pulp-platform/fmc_peripheral_boards/05_FMC_4_Hyperram_32MB/Documentation/FMC_4Hyperram_board_LAY.PDF

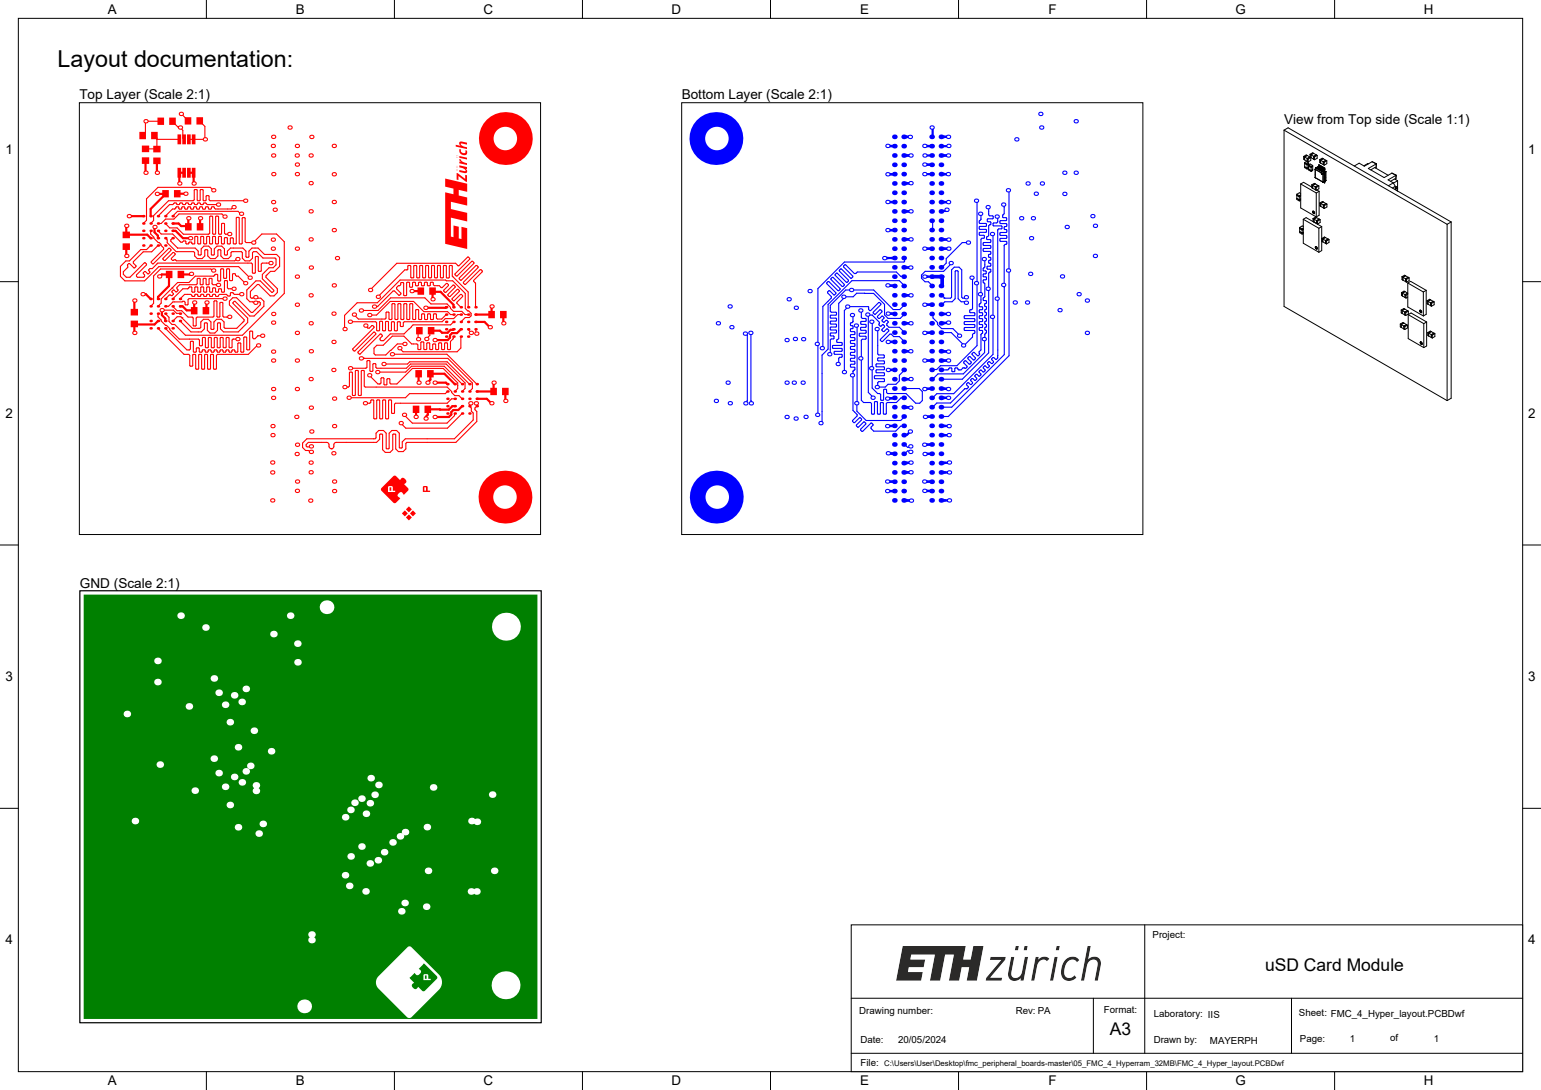
[picture p35: page 1]

View from Top side (Scale 1:1)

Project: uSD Card Module

Drawing number: Rev: PA Date: 20/05/2024 | Format: | Laboratory: IIS Drawn by: MAYERPH | Sheet: FMC_4_Hyper_layout.PCBDwf of A3 Page: 1 1

File:
C:\Users\User\Desktop\fmc_peripheral_boards-master\05_FMC_4_Hyperram_32MB\FMC_4_Hyper_layout.PCBDwf
