pulp-platform/fmc_peripheral_boards/05_FMC_4_Hyperram_32MB/Documentation/FMC_4Hyperram_board_SCH.pdf

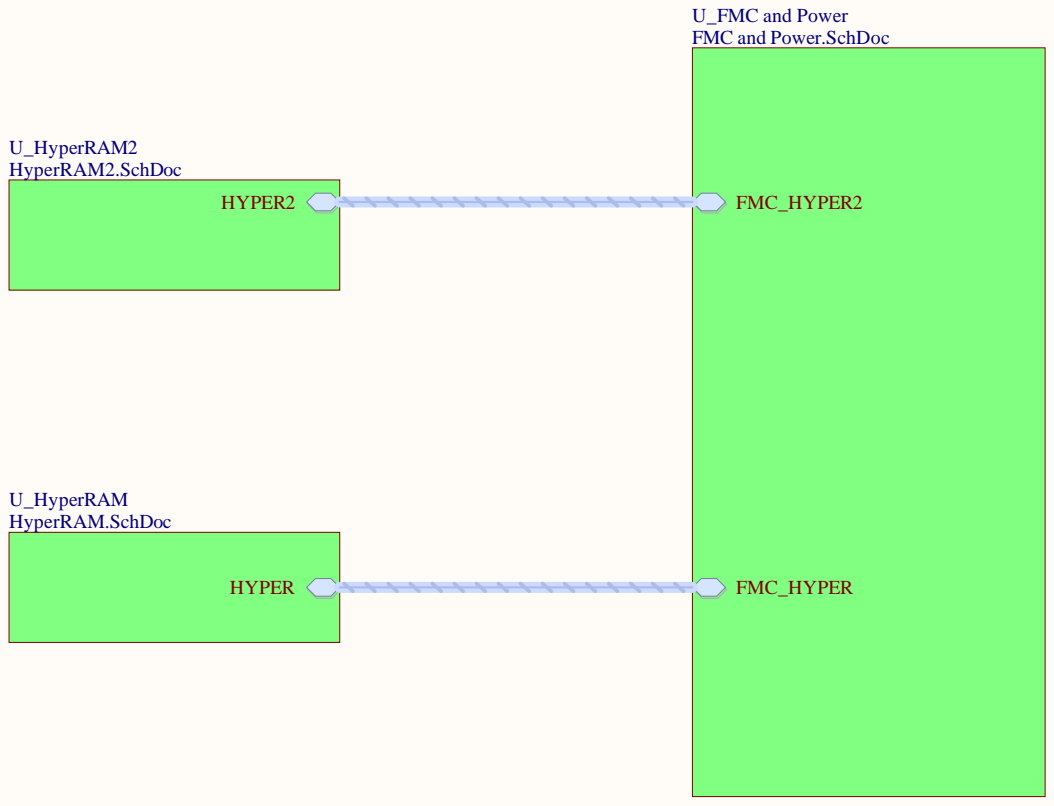
[picture p36: page 1]

U_FMC and Power
FMC and Power.SchDoc

Project: Pulp FMC Sensor Board

Drawing number: Rev: * Date: 20/05/2024 14:07:33 | Format: A4 Q | Laboratory: Microelectronics Design Center Drawn by: A. Blanco Fontao | Sheet: Page 1 of 7

C:\Users\User\Desktop\fmc_peripheral_boards-master\05_FMC_4_Hyperram_32MB\FMC_4Hyperram_board.SchDoc

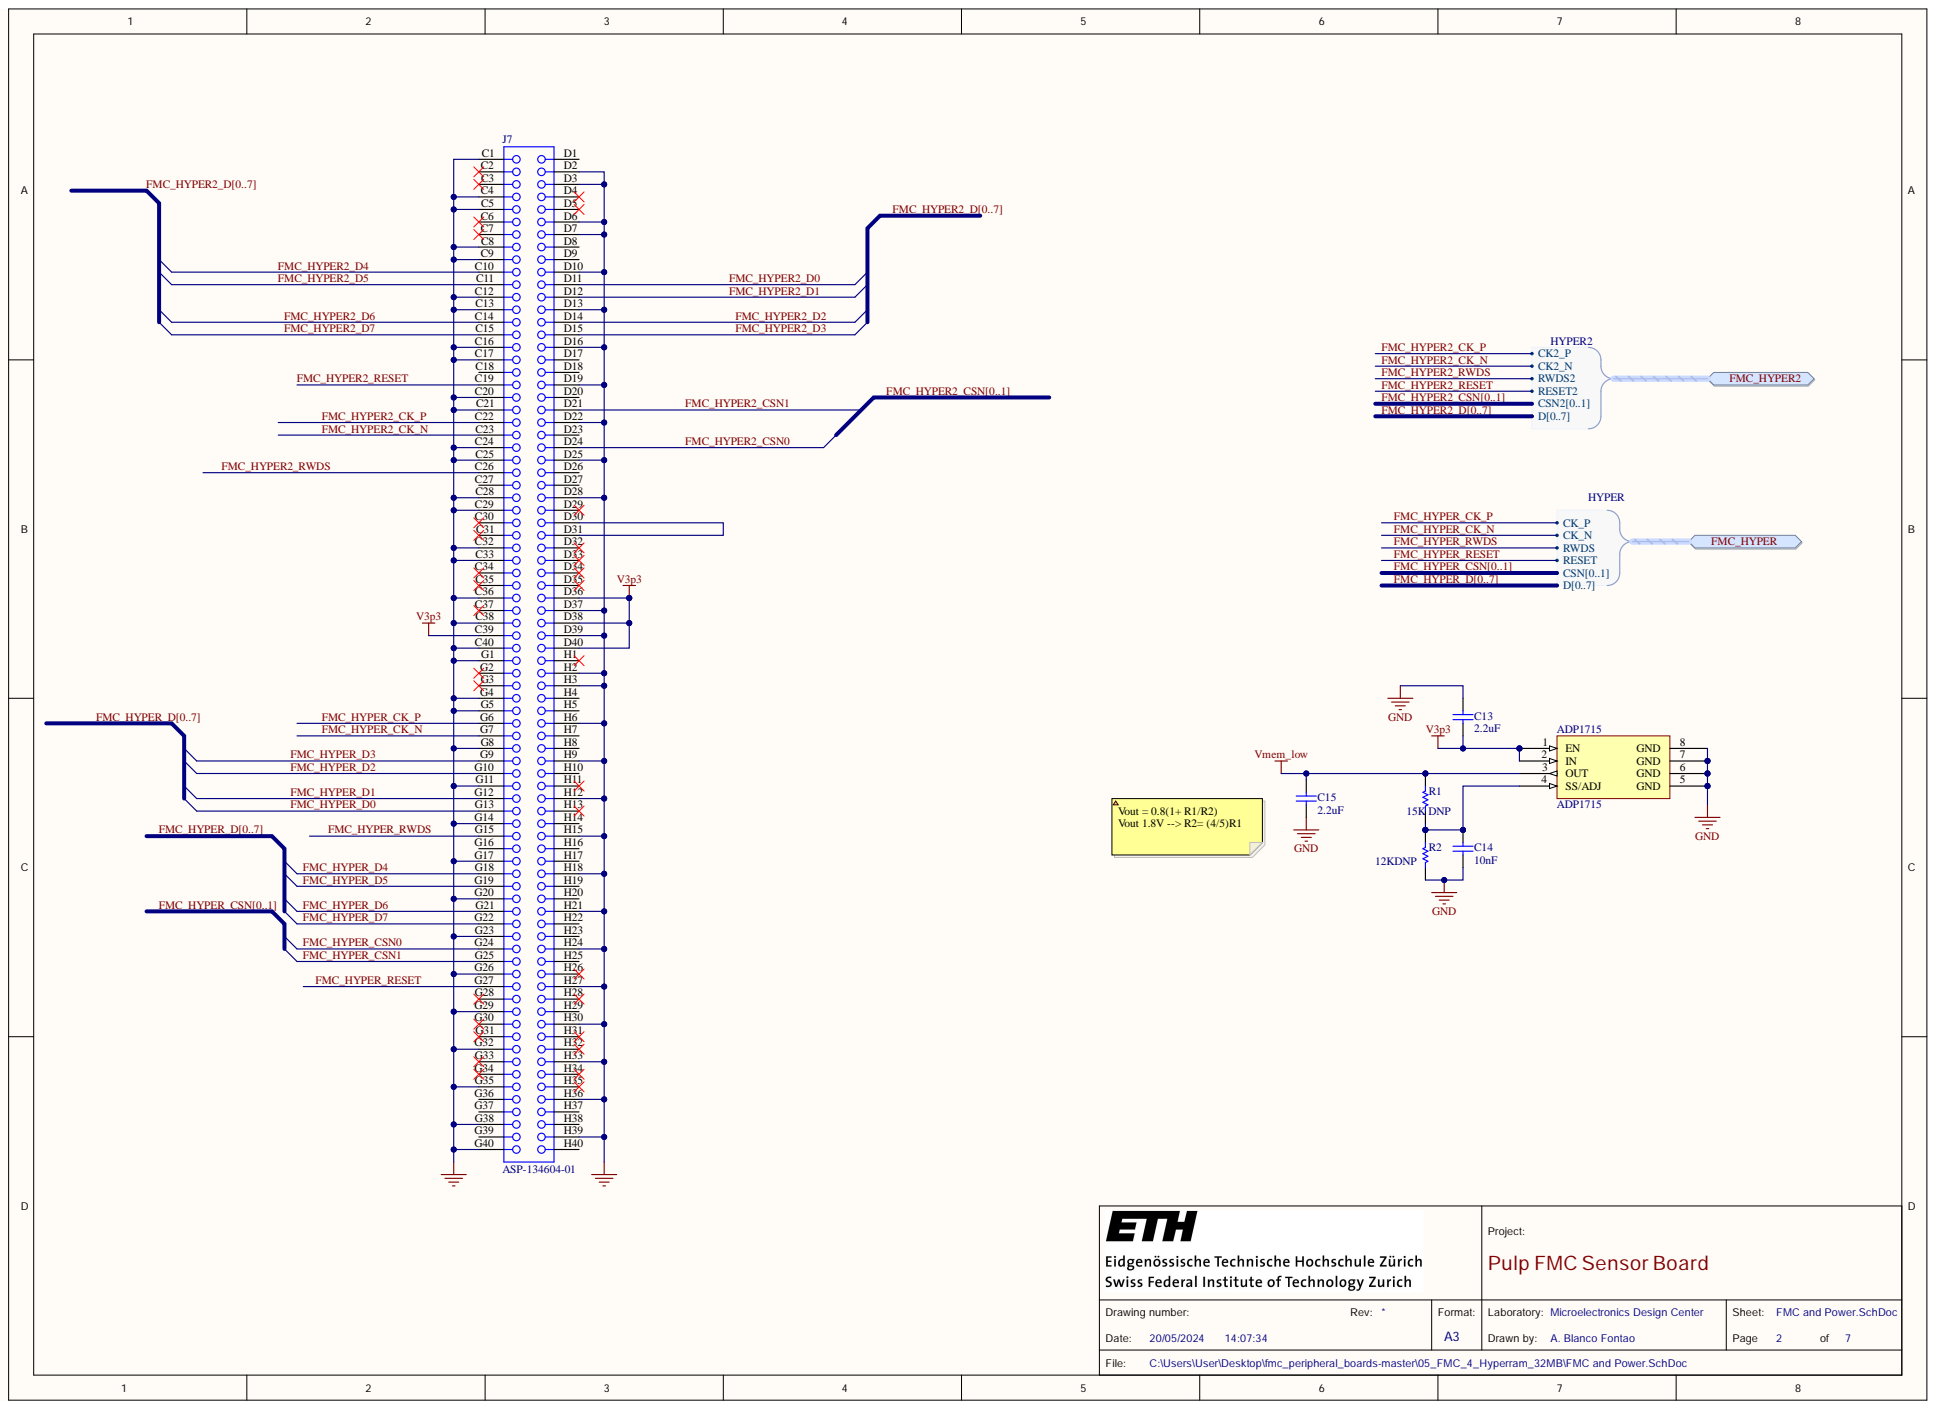
[picture p37: page 2]

C2 | | D2
C3 | | D3
C4 | | D4
C5 | | D5
C6 | | D6
C7 | | D7
C8 | | D8
C9 | | D9
C10 C11 C12 | | D10

C13
C14 C15 C16 | D14 D15 D16

C21 | | D21 D22
C22 C23 C24

C25
C26 C27 | | D26

C28 | | D28
C29 | | D29
C30 | | D30
C31 | | D31
C32 | | D32 | | V3p3
C33 | | D33
C34 | | D34
C35 | | D35
C36 | | D36
C37 | | D37
C38 | | D38
C39 | | D39
C40 | | D40
G1 | | H1
G2 | | H2
G3 | | H3
G4 | | H4

G6 G7 G8 | H6 | GND

G17 | | H17
G18 G19 G20 | | H18

G29 | | H29
G30 | | H30
G31 | | H31
G32 | | H32
G33 | | H33
G34 | | H34
G35 | | H35
G36 | | H36
G37 | | H37
G38 | | H38
G39 | | H39
G40 | | H40

Project: Pulp FMC Sensor Board

Drawing number: Rev: * Date: 20/05/2024 14:07:34 | Format: A3 | Laboratory: Microelectronics Design Center Drawn by: A. Blanco Fontao | Sheet: FMC and Power.SchDoc Page 2 of 7

C:\Users\User\Desktop\fmc_peripheral_boards-master\05_FMC_4_Hyperram_32MB\FMC and Power.SchDoc

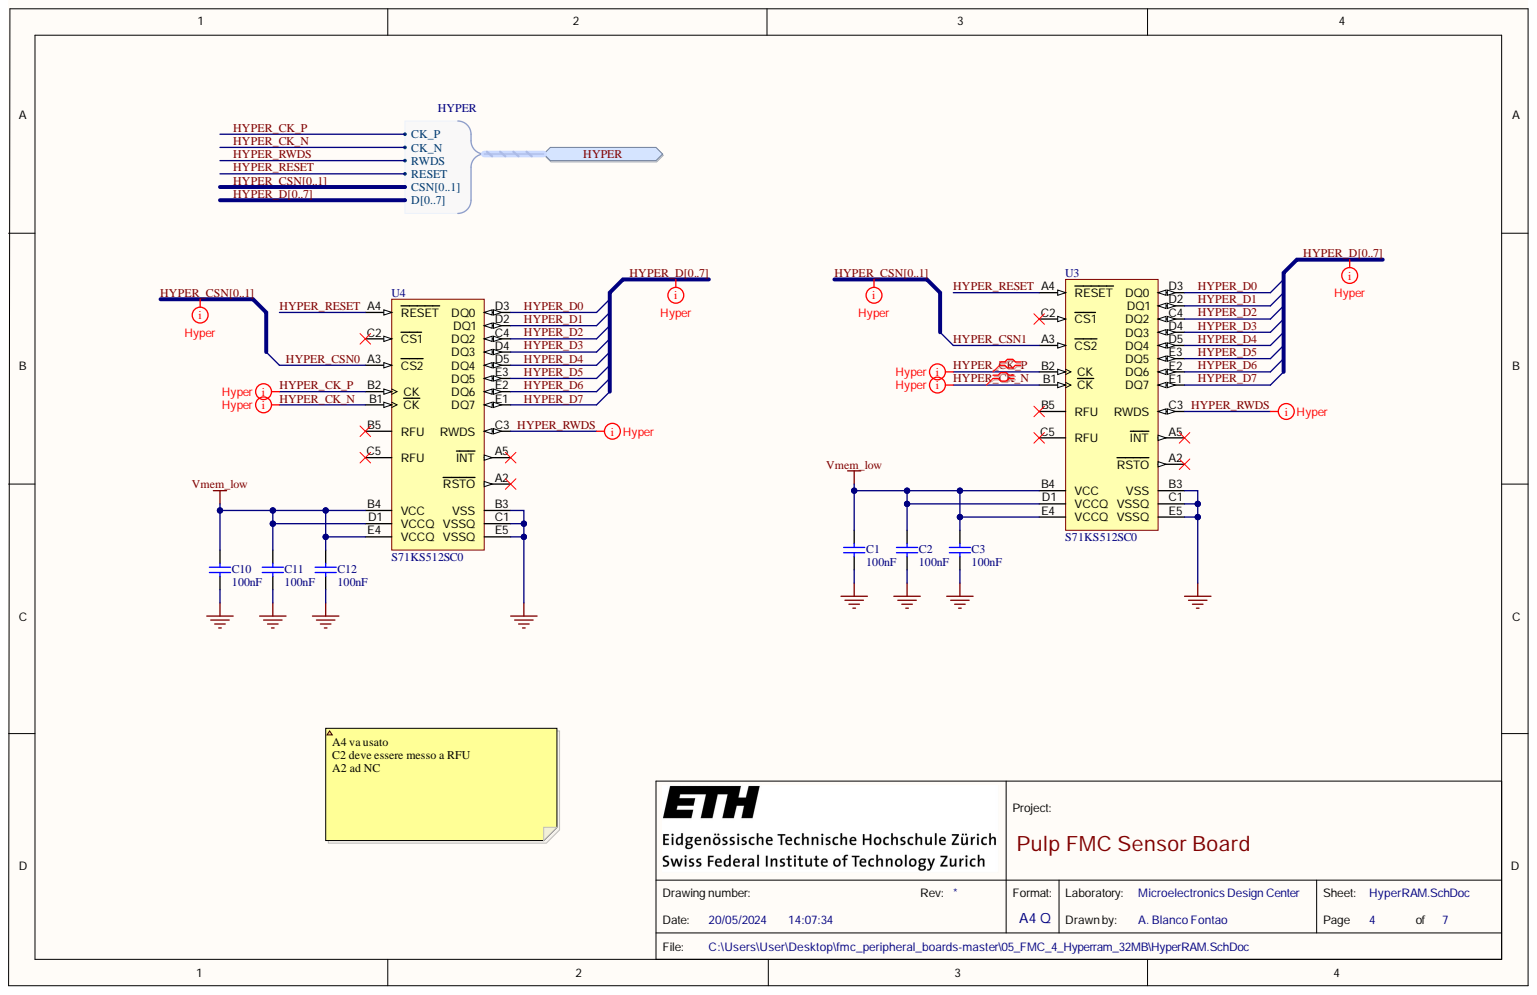
[picture p38: page 3]

A4 va usato
C2 deve essere messo a RFU

Project: Pulp FMC Sensor Board

Drawing number: Rev: * Date: 20/05/2024 14:07:34 | Format: A4 Q | Laboratory: Microelectronics Design Center Drawn by: A. Blanco Fontao | Sheet: HyperRAM.SchDoc Page 4 of 7

C:\Users\User\Desktop\fmc_peripheral_boards-master\05_FMC_4_Hyperram_32MB\HyperRAM.SchDoc

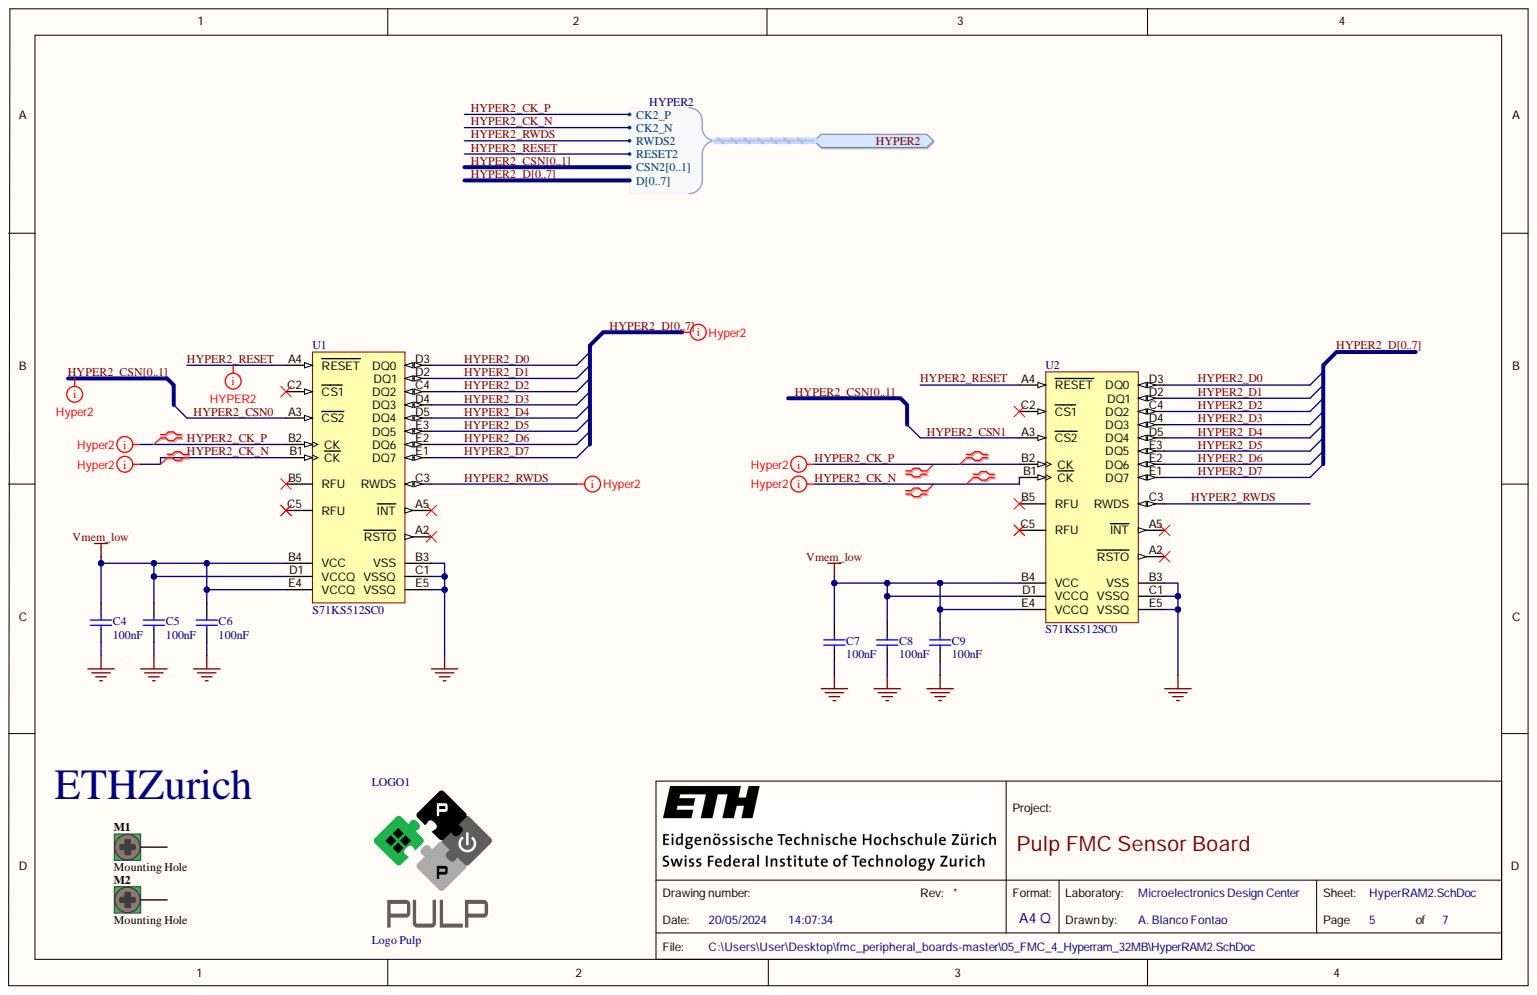
[picture p39: page 4]

Project: Pulp FMC Sensor Board

Drawing number: Rev: * Date: 20/05/2024 14:07:34 | Format: A4 Q | Laboratory: Microelectronics Design Center Drawn by: A. Blanco Fontao | Sheet: HyperRAM2.SchDoc Page 5 of 7

C:\Users\User\Desktop\fmc_peripheral_boards-master\05_FMC_4_Hyperram_32MB\HyperRAM2.SchDoc

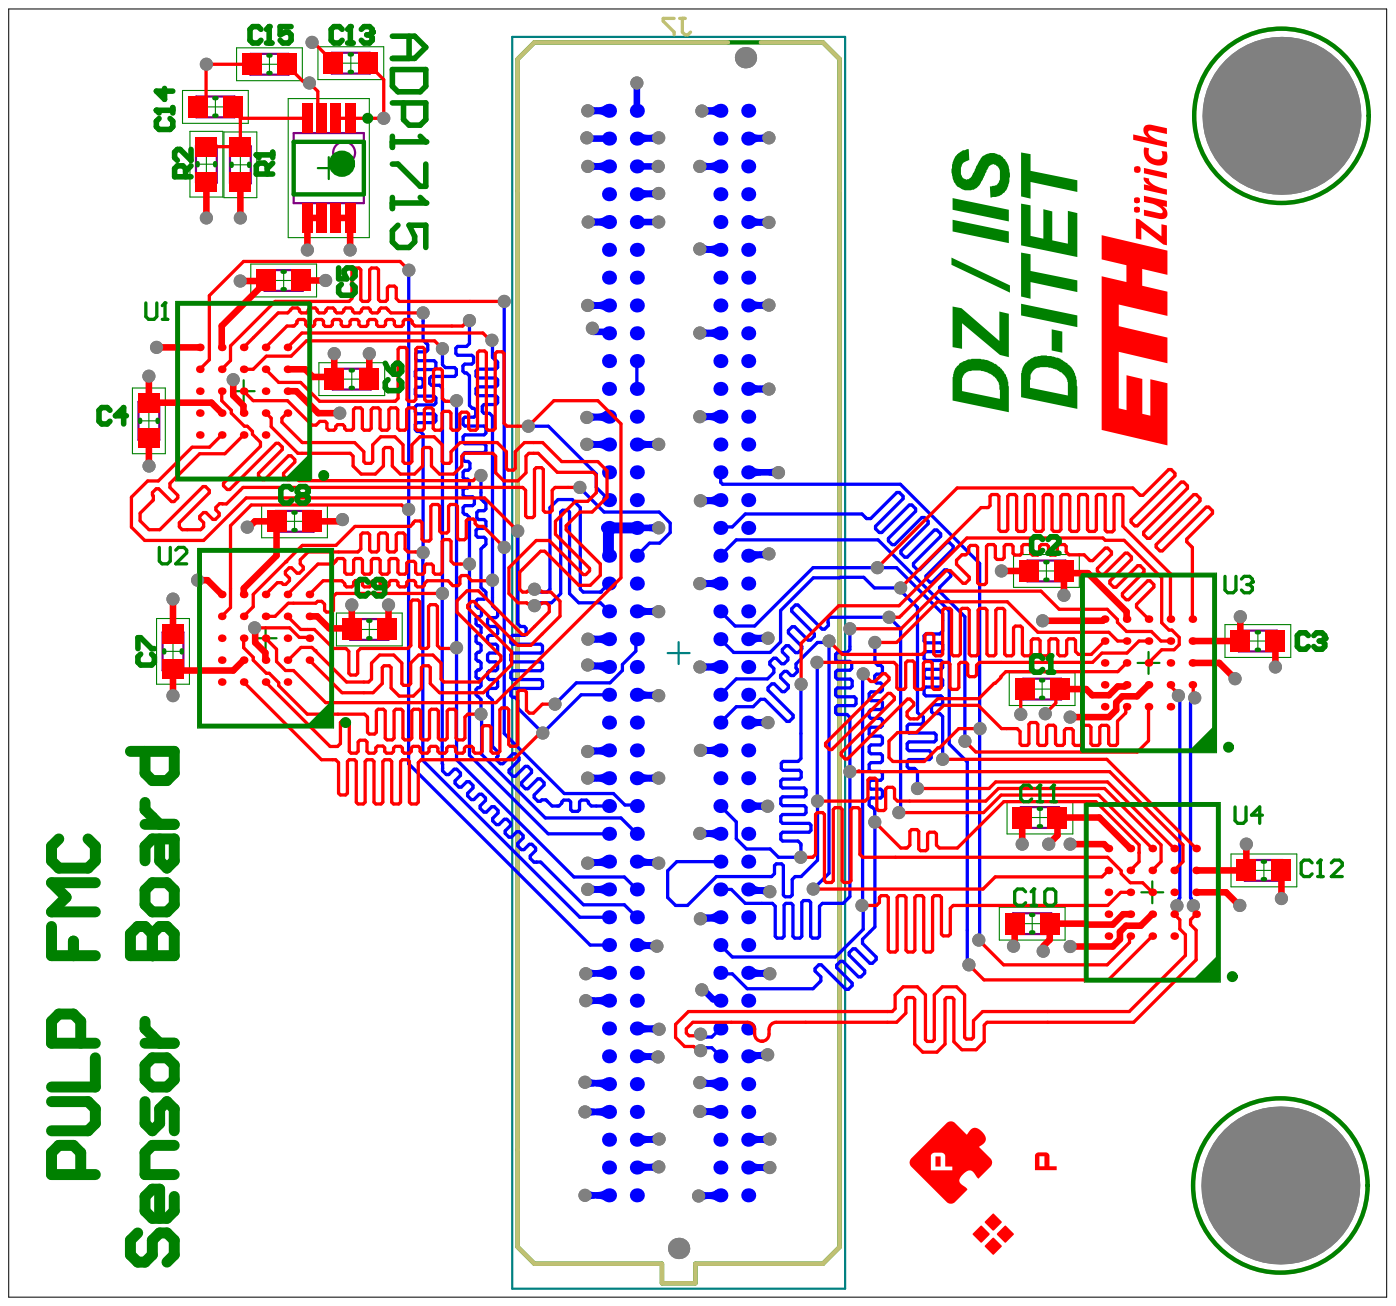
[picture p40: page 5]
