pulp-platform/fmc_peripheral_boards/01_Carrier_Board/Documentation/FPGA_Peripheral_Board_CON.PDF

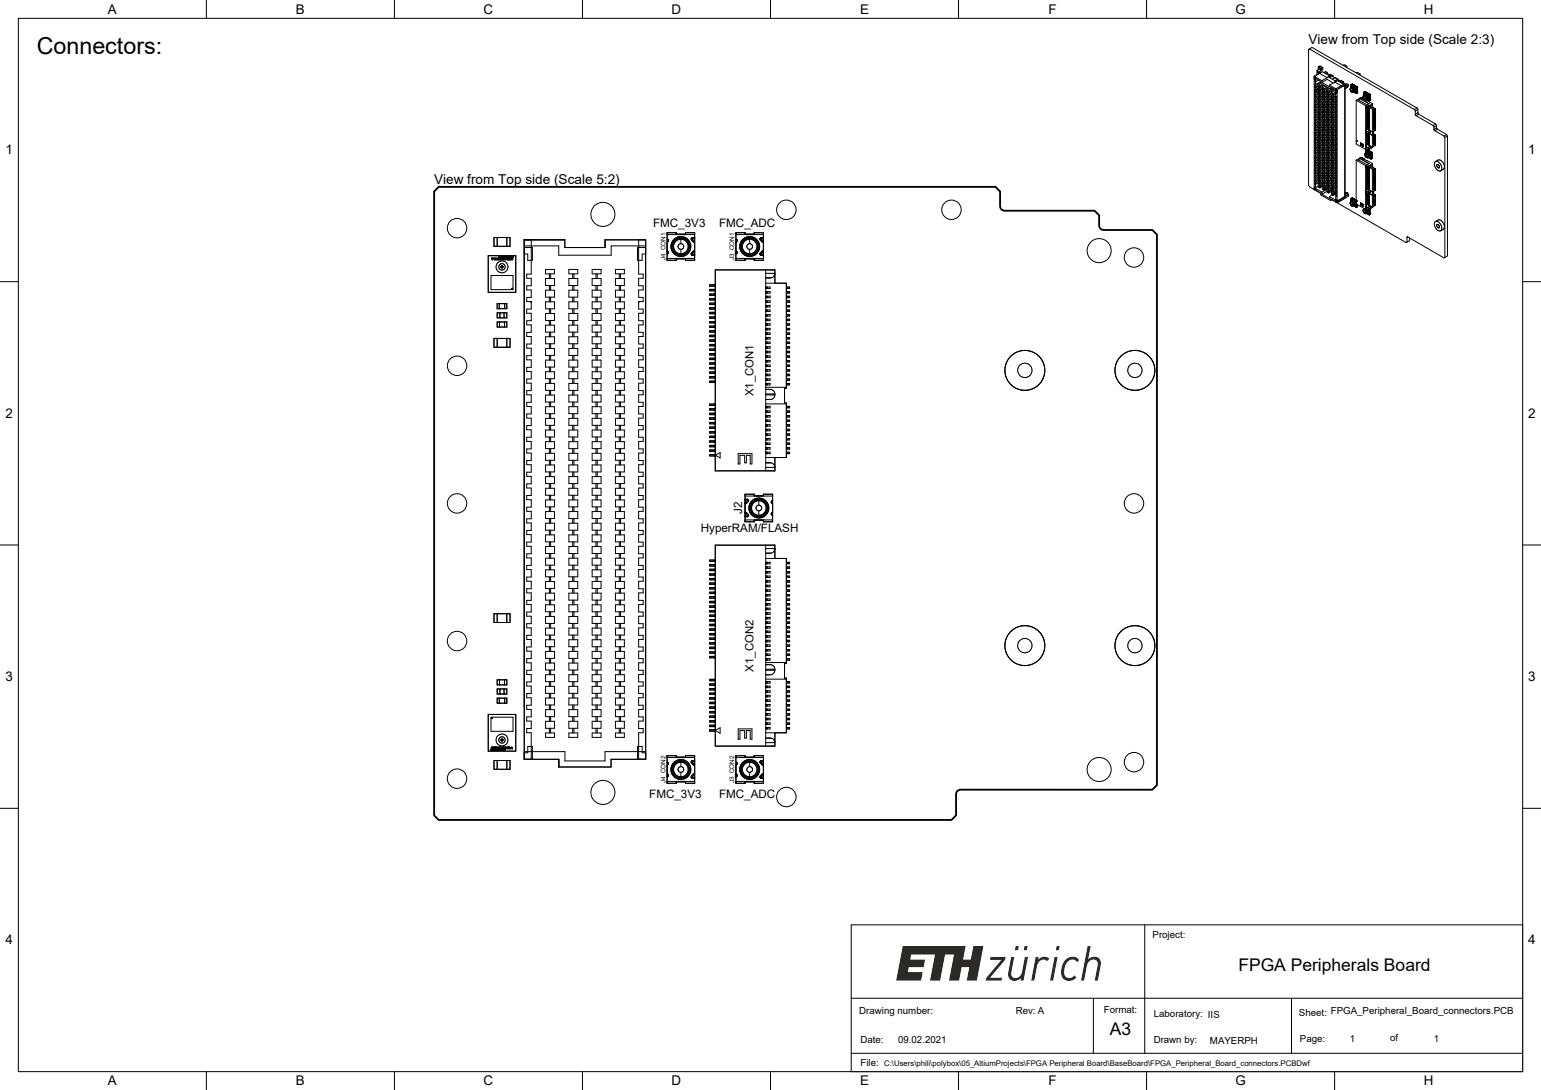
[picture p43: page 1]

View from Top side (Scale 2:3)

View from Top side (Scale 5:2)

File:
C:\Users\phili\polybox\05_AltiumProjects\FPGA Peripheral Board\BaseBoard\FPGA_Peripheral_Board_connectors.PCBDwf
