pulp-platform/fmc_peripheral_boards/01_Carrier_Board/Documentation/FPGA_Peripheral_Board_FAB.PDF

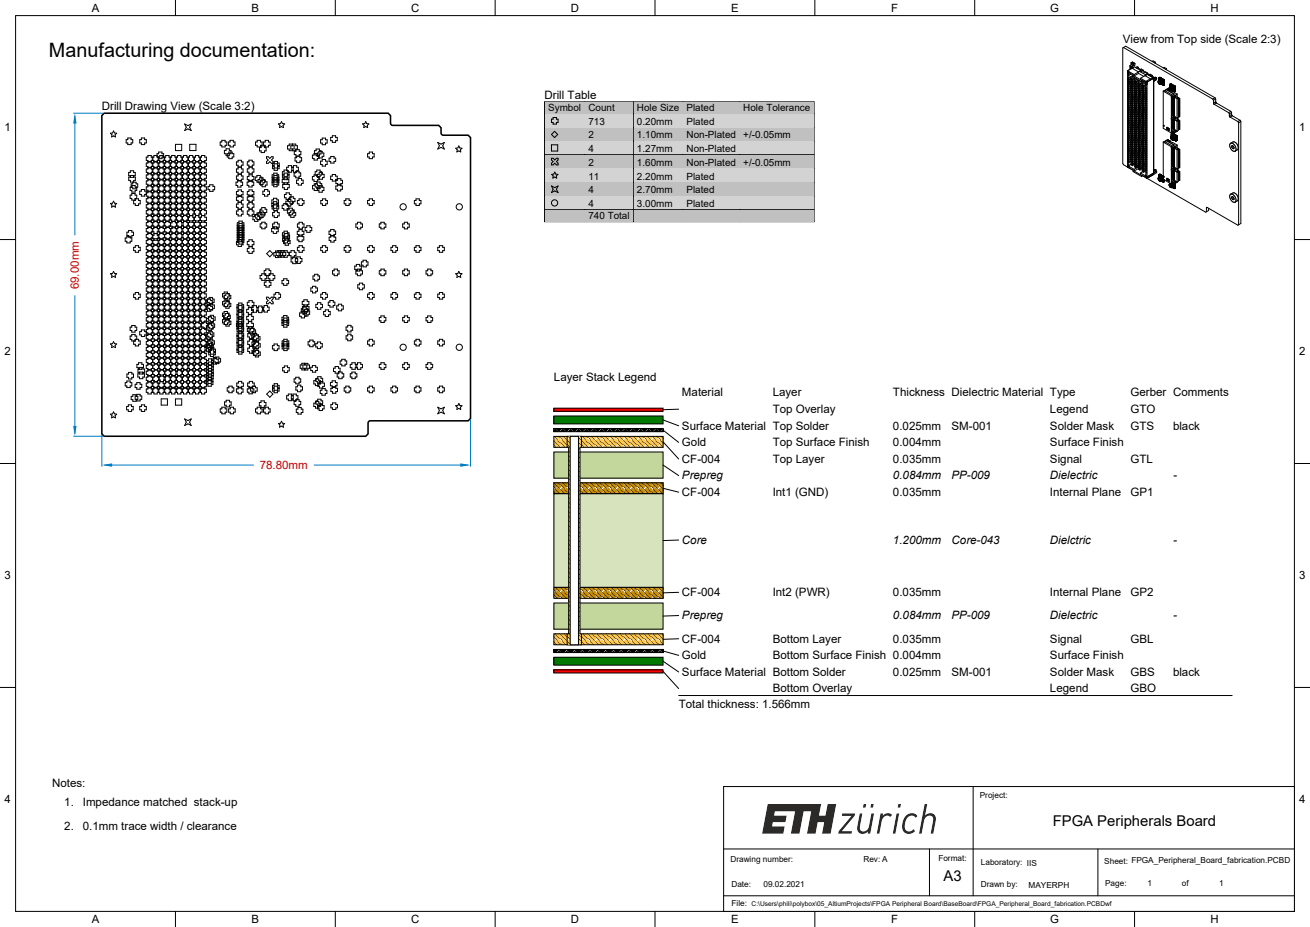
[picture p44: page 1]

View from Top side (Scale 2:3)

Drill Drawing View (Scale 3:2)

Notes:
1. Impedance matched stack-up

File:
C:\Users\phili\polybox\05_AltiumProjects\FPGA Peripheral Board\BaseBoard\FPGA_Peripheral_Board_fabrication.PCBDwf
