pulp-platform/fmc_peripheral_boards/01_Carrier_Board/Documentation/FPGA_Peripheral_Board_LAY.PDF

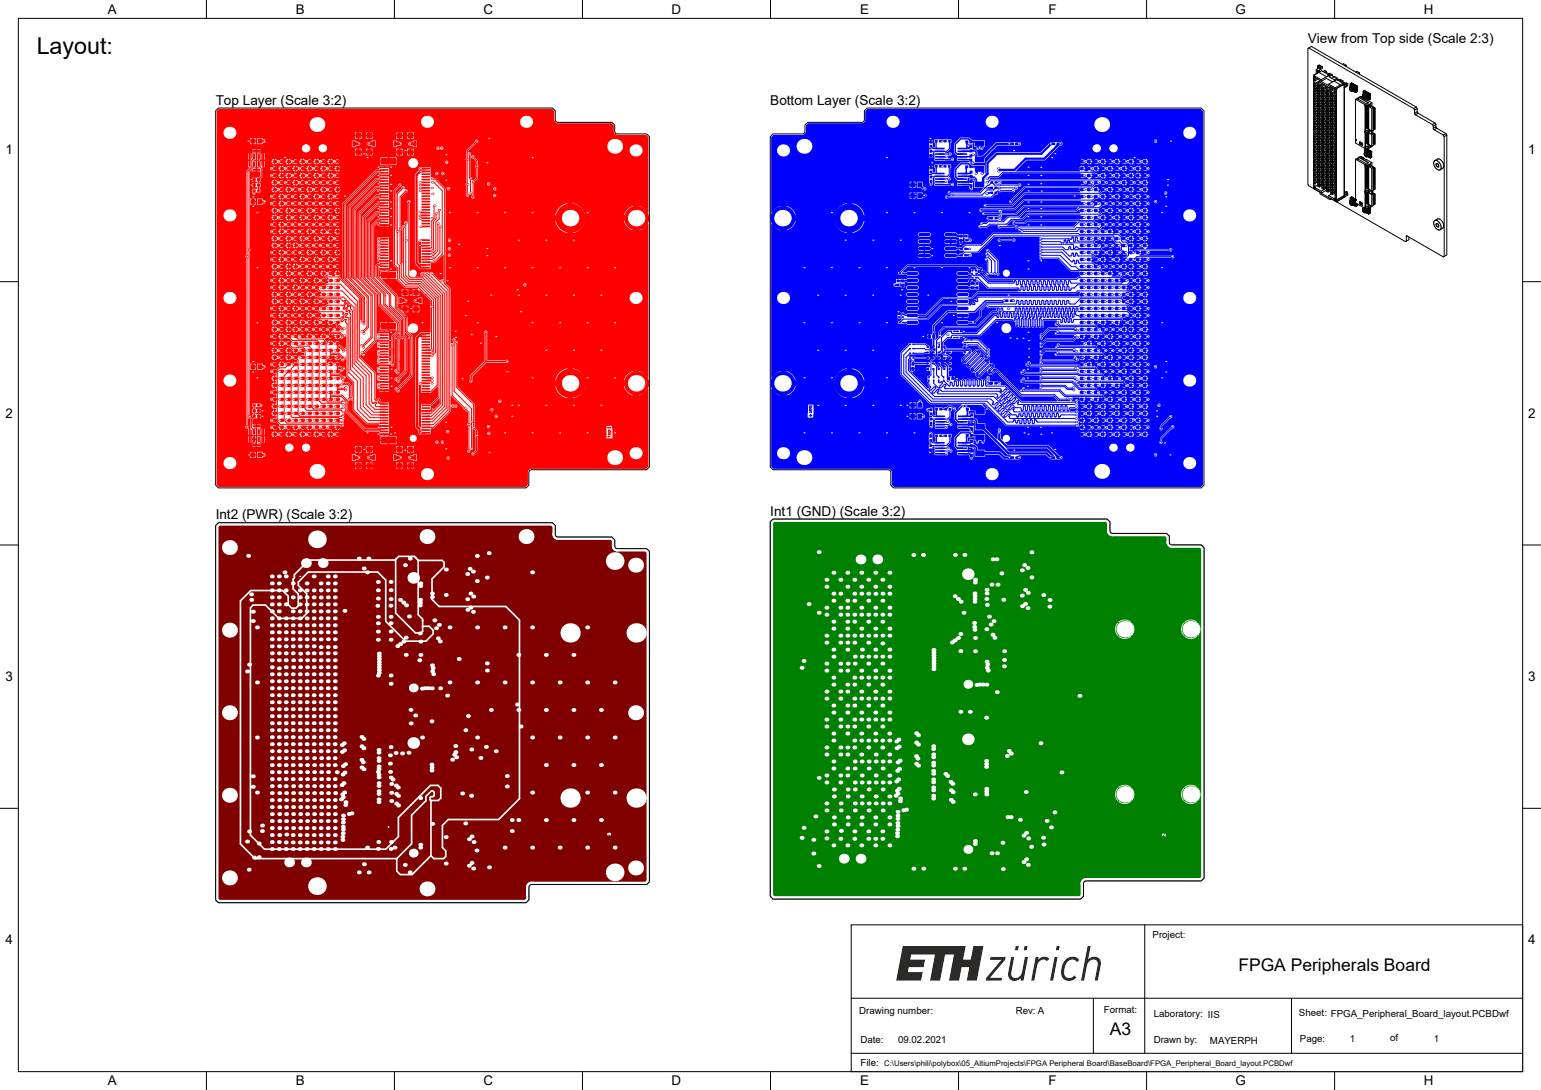
[picture p45: page 1]

View from Top side (Scale 2:3)

File:
C:\Users\phili\polybox\05_AltiumProjects\FPGA Peripheral Board\BaseBoard\FPGA_Peripheral_Board_layout.PCBDwf
