pulp-platform/fmc_peripheral_boards/01_Carrier_Board/Documentation/FPGA_Peripheral_Board_SCH.PDF

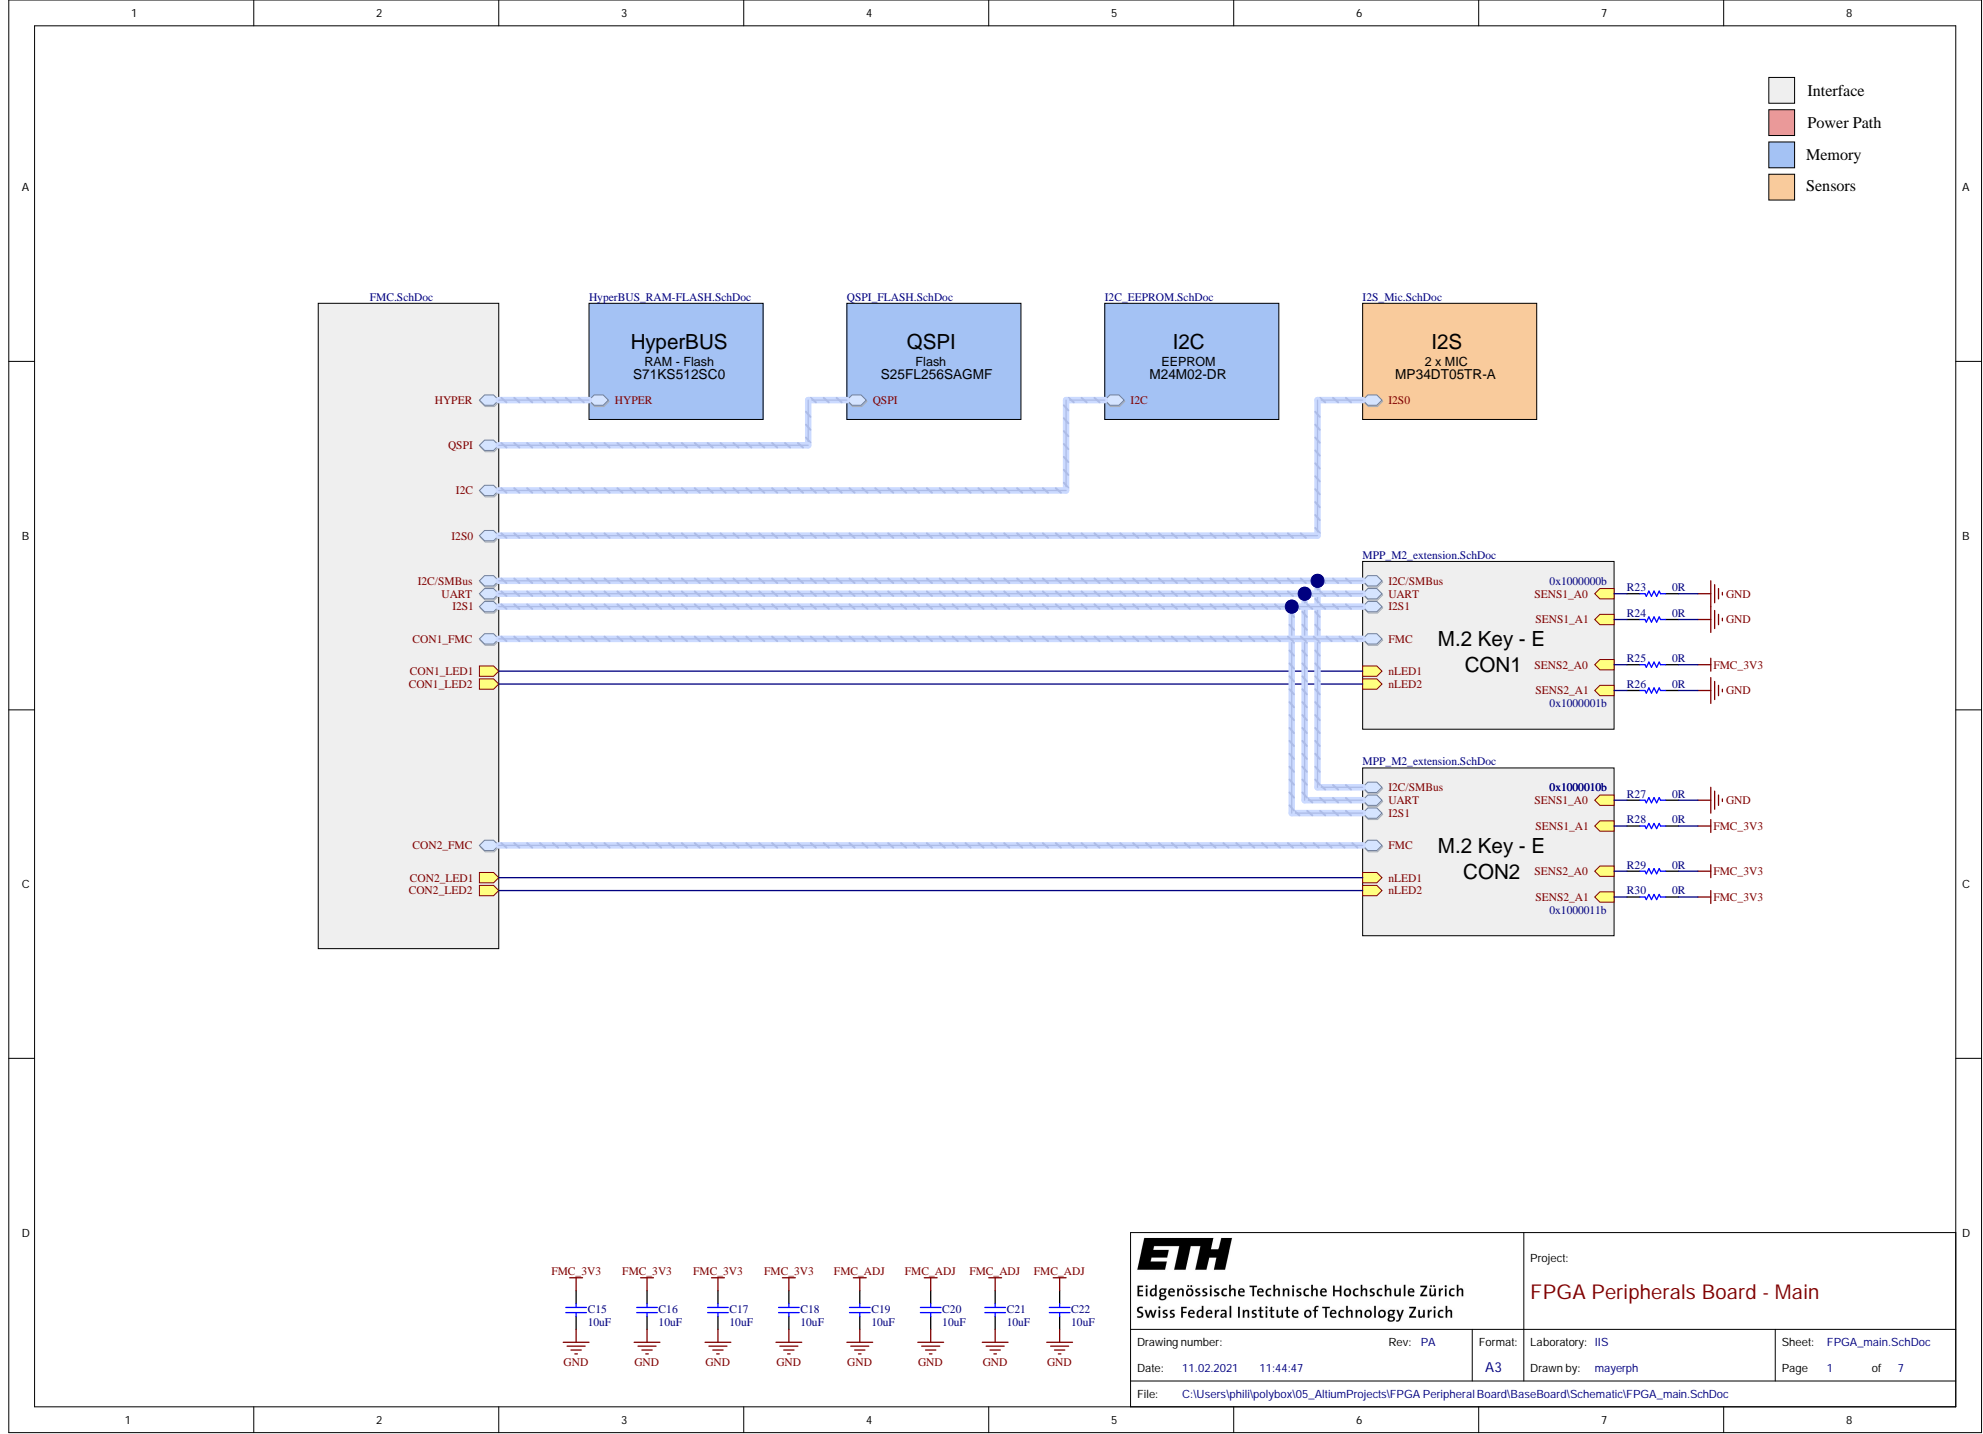
[picture p46: page 1]

FMC.SchDoc HyperBUS_RAM-FLASH.SchDoc QSPI_FLASH.SchDoc I2C_EEPROM.SchDoc I2S_Mic.SchDoc

Project: FPGA Peripherals Board - Main

Drawing number: Rev: PA Date: 11.02.2021 11:44:47 | Format: A3 | Laboratory: IIS Drawn by: mayerph | Sheet: FPGA_main.SchDoc Page 1 of 7

C:\Users\phili\polybox\05_AltiumProjects\FPGA Peripheral Board\BaseBoard\Schematic\FPGA_main.SchDoc

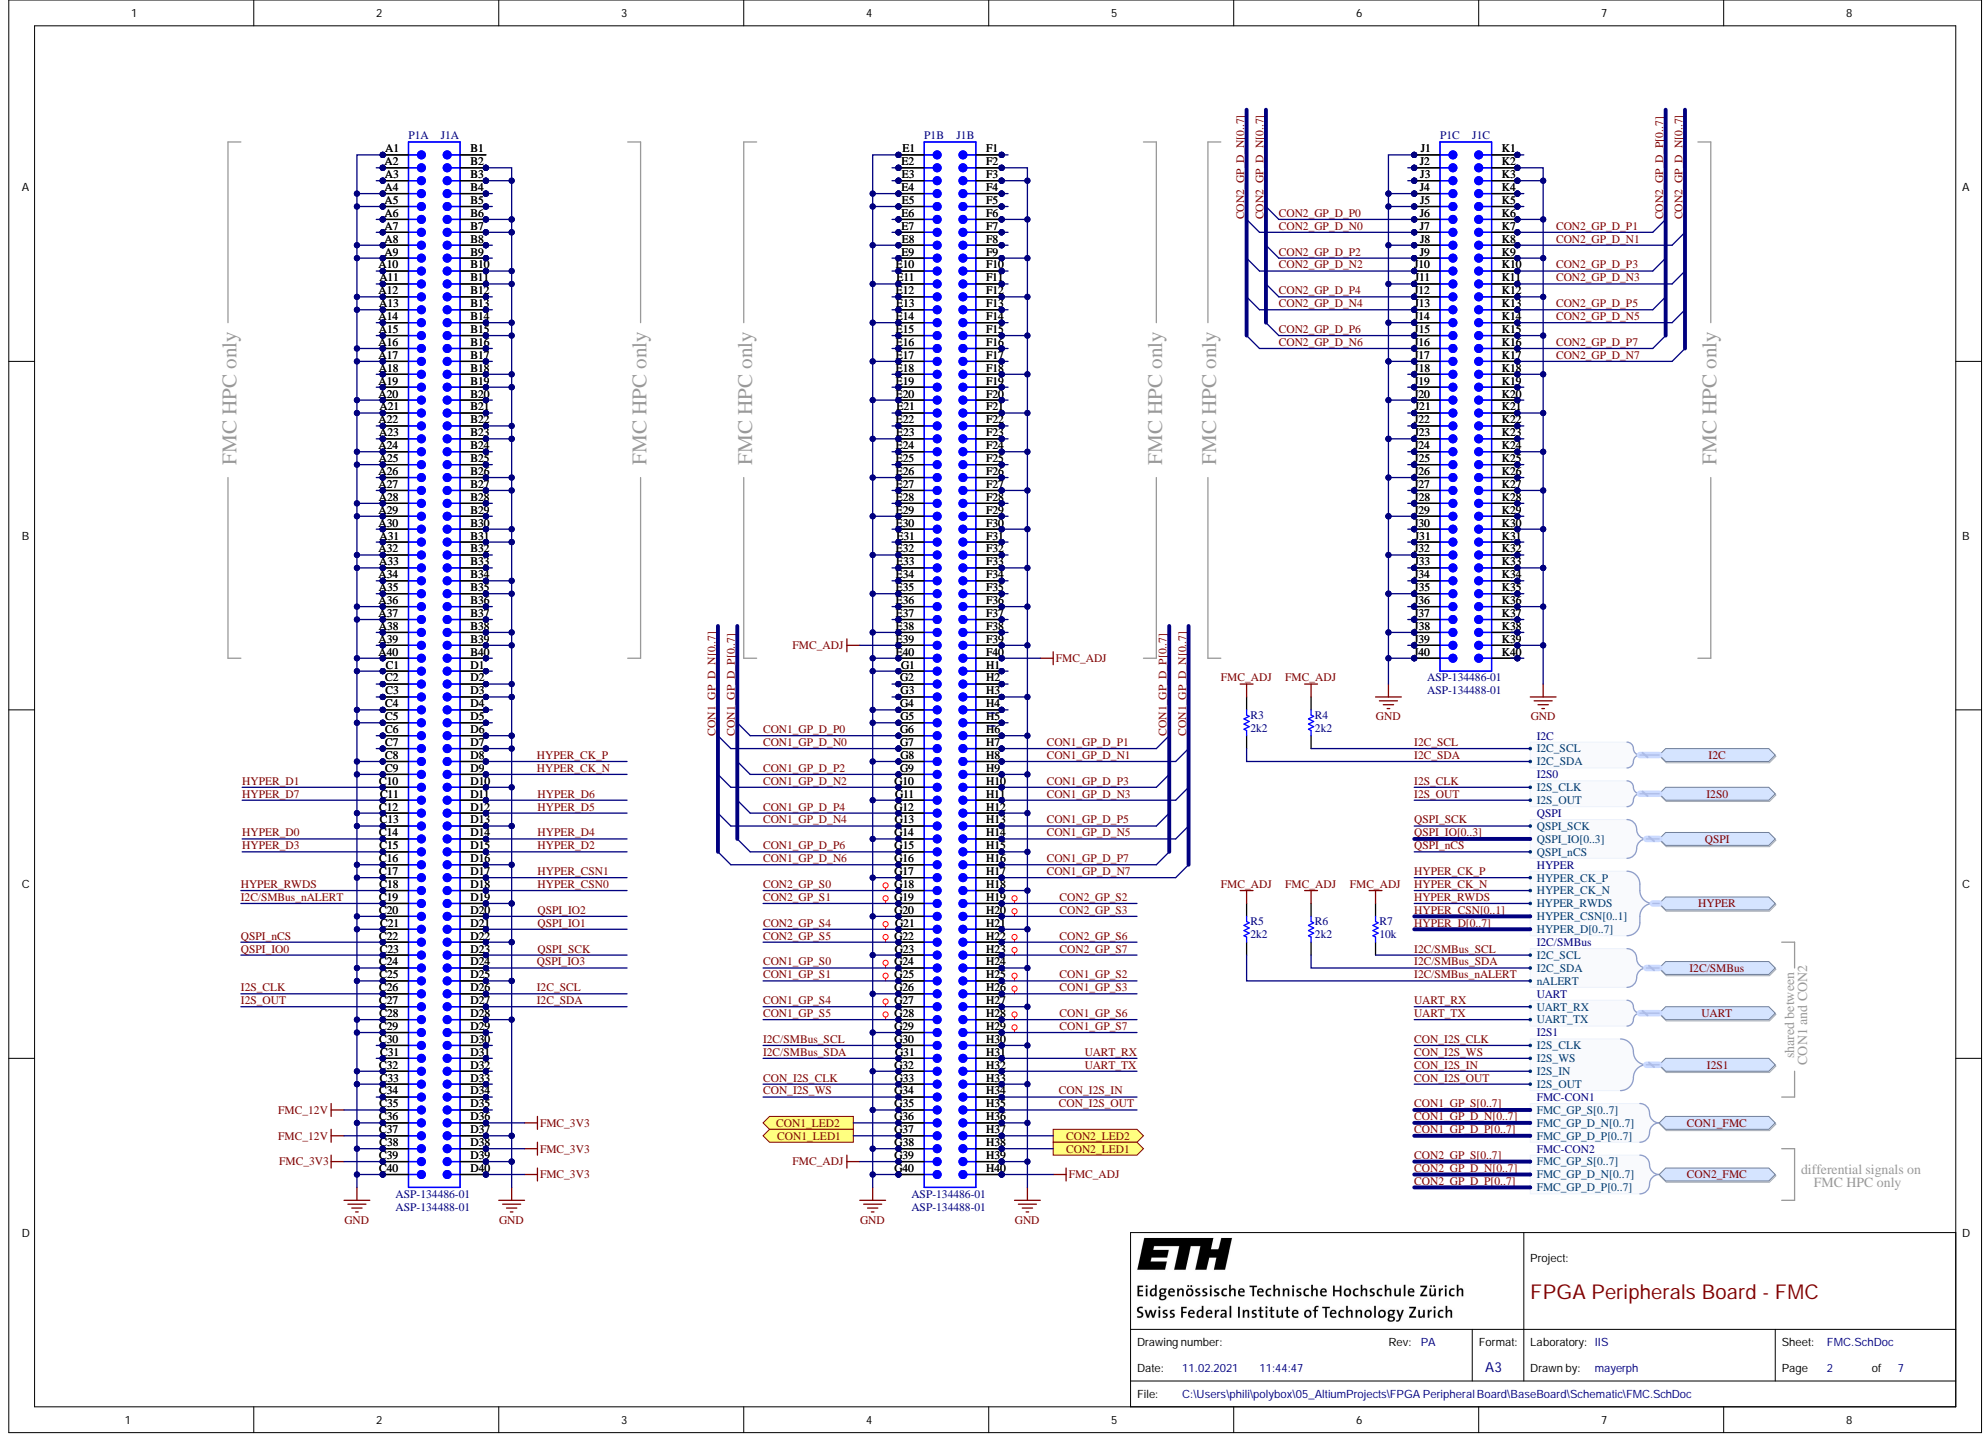
[picture p47: page 2]

CON1 and CON2 differential signals on FMC HPC only

Project: FPGA Pe rip h e rals Bo a rd - FMC

Drawin g n umb er: | Forma t: | L a b oratory: IIS Drawn by: | Sh eet: FMC.SchDoc Page 2 of

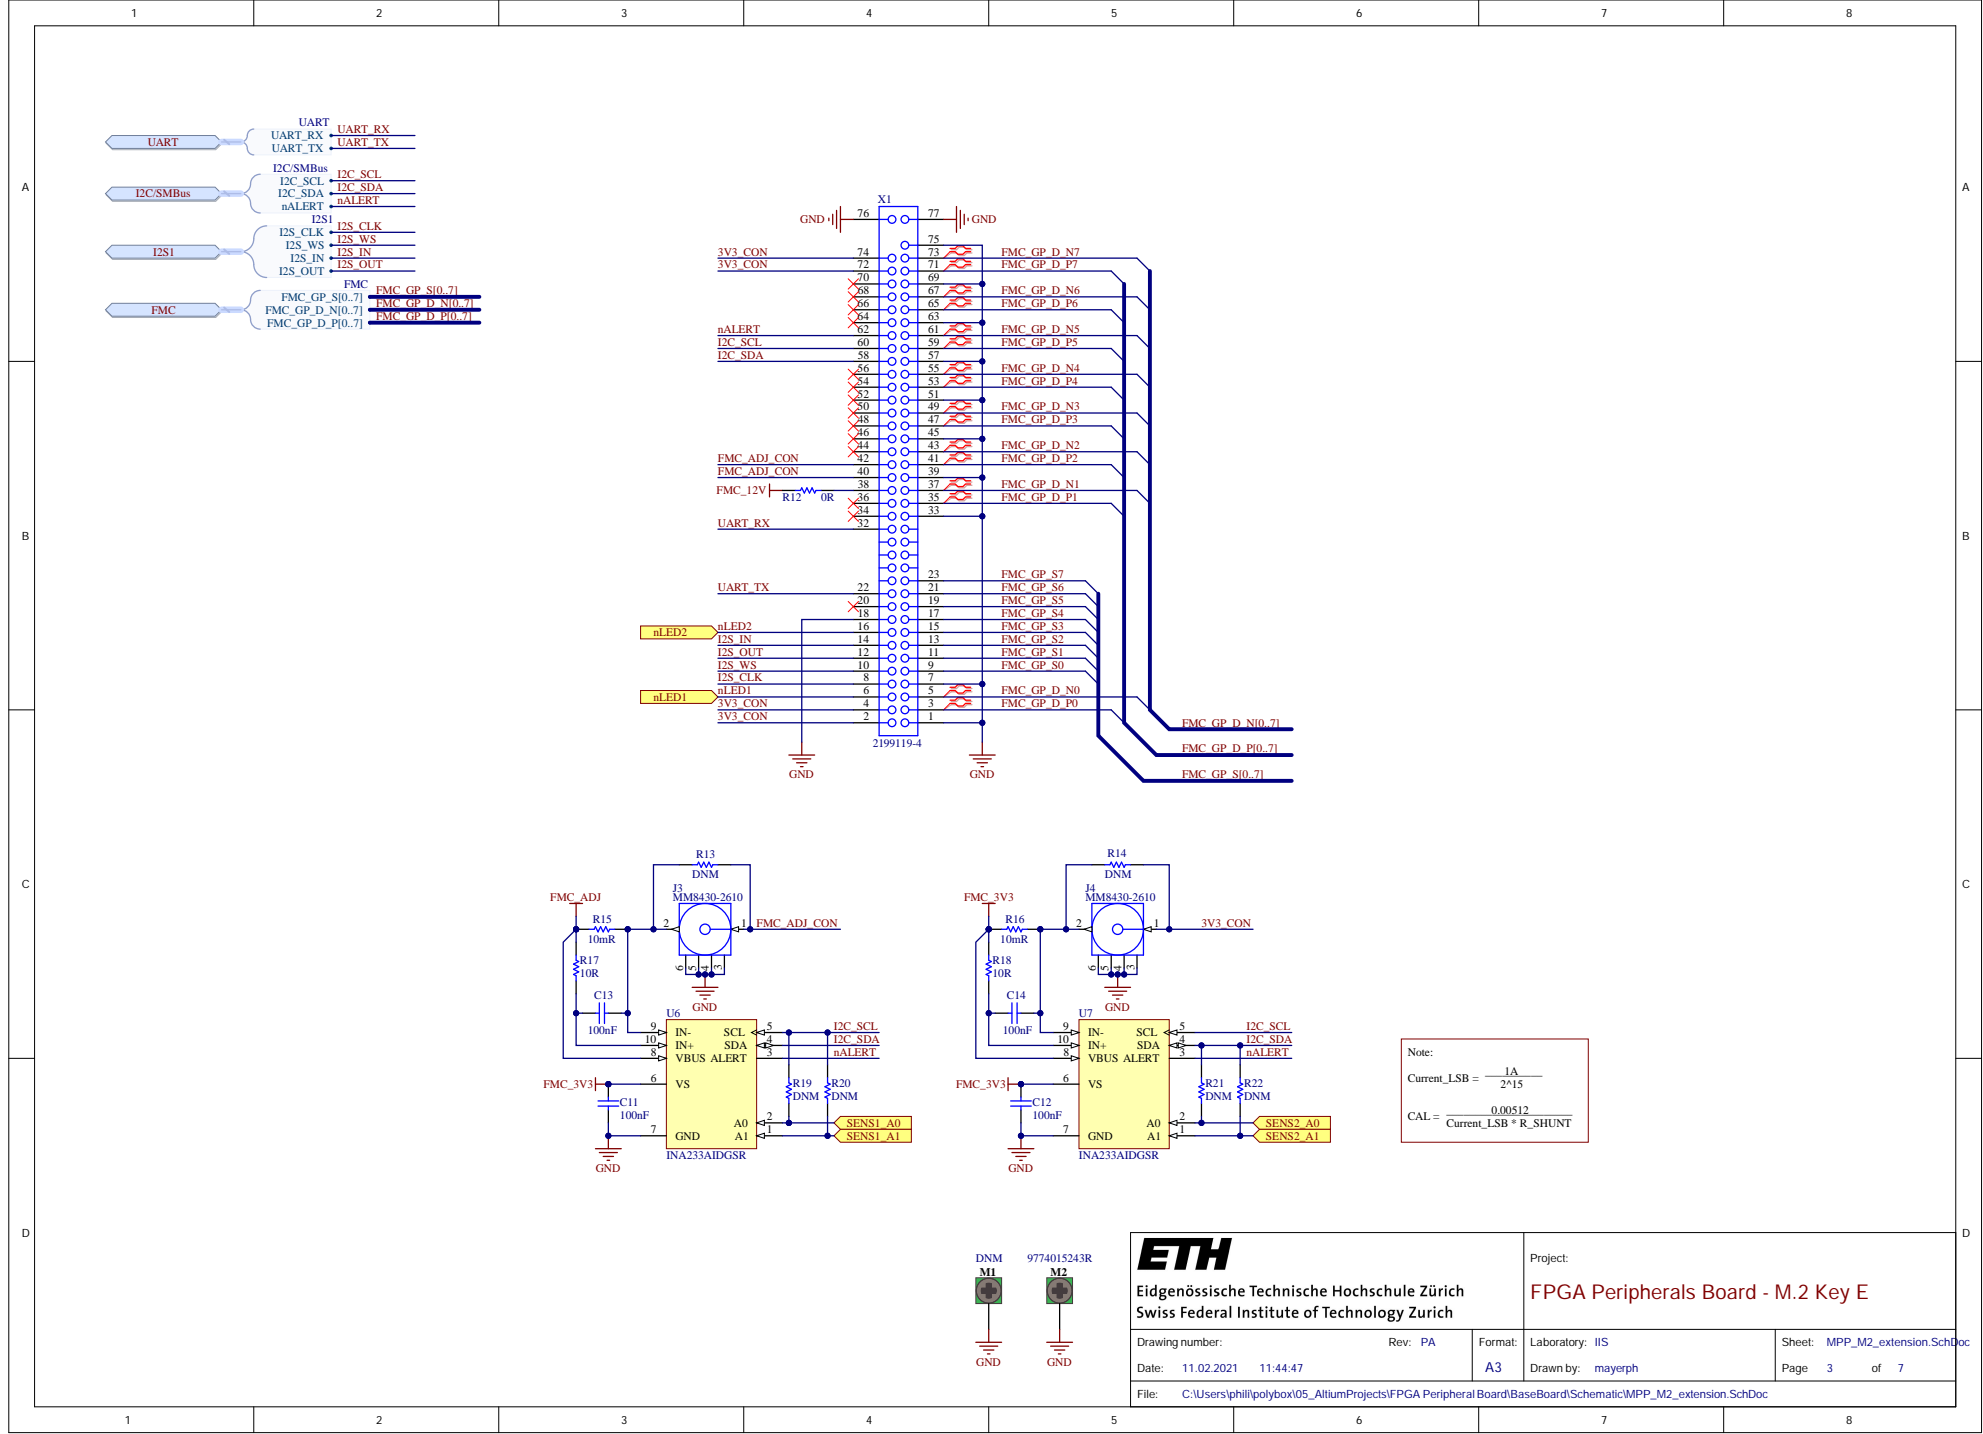
[picture p48: page 3]

Project: FPGA Peripherals Board - M.2 Key E

Drawing number: | Format: | Laboratory: IIS | Sheet: MPP_M2_extension.SchDoc Page 3 of 7

C:\Users\phili\polybox\05_AltiumProjects\FPGA Peripheral Board\BaseBoard\Schematic\MPP_M2_extension.SchDoc

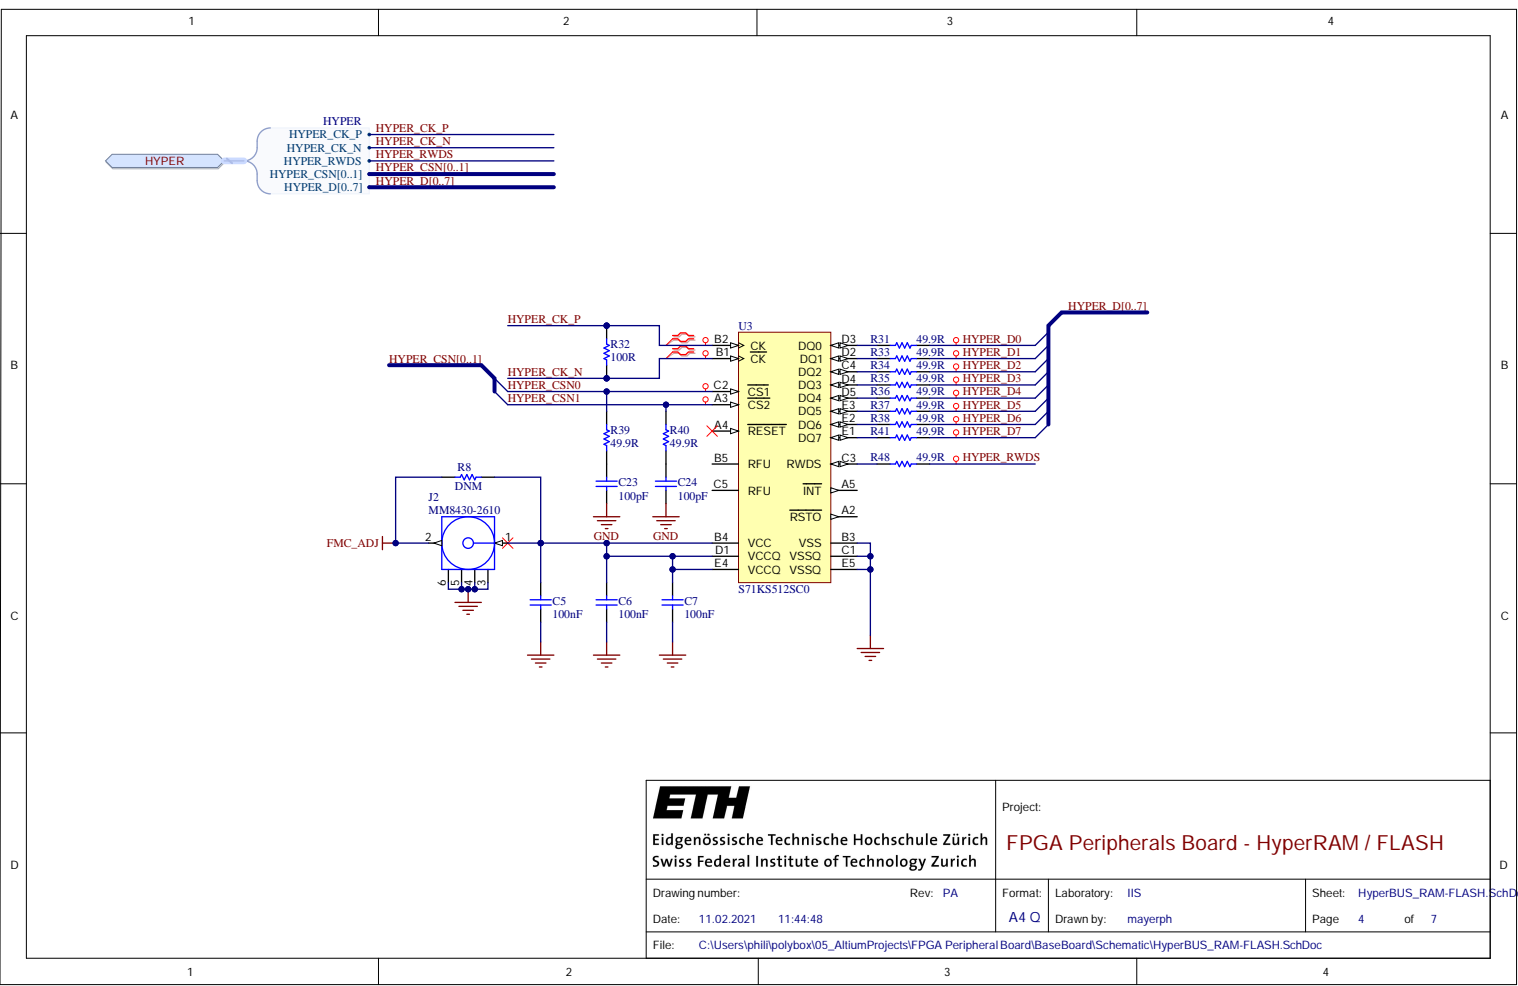
[picture p49: page 4]

Project: FPGA Peripherals Board - HyperRAM / FLASH

Drawing number: Rev: PA | Format: A4 Q | Laboratory: IIS | Sheet: Page 4 of 7

C:\Users\phili\polybox\05_AltiumProjects\FPGA Peripheral Board\BaseBoard\Schematic\HyperBUS_RAM-FLASH.SchDoc

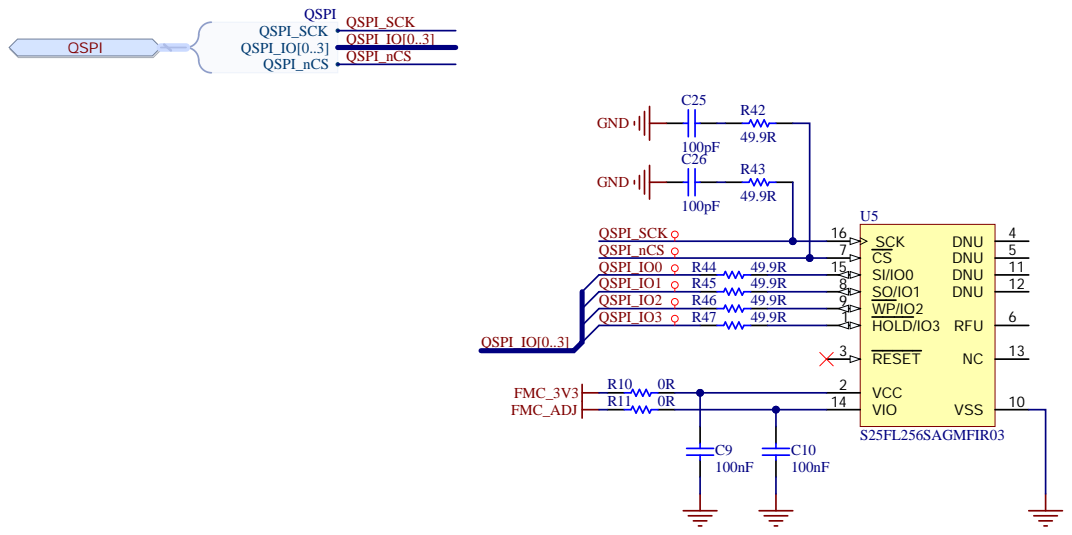
[picture p50: page 5]

Project: FPGA Peripherals Board - FLASH

Drawing number: Rev: PA | Format: A4 Q | Laboratory: IIS | Sheet: QSPI_FLASH.SchDoc Page 5 of 7

C:\Users\phili\polybox\05_AltiumProjects\FPGA Peripheral Board\BaseBoard\Schematic\QSPI_FLASH.SchDoc

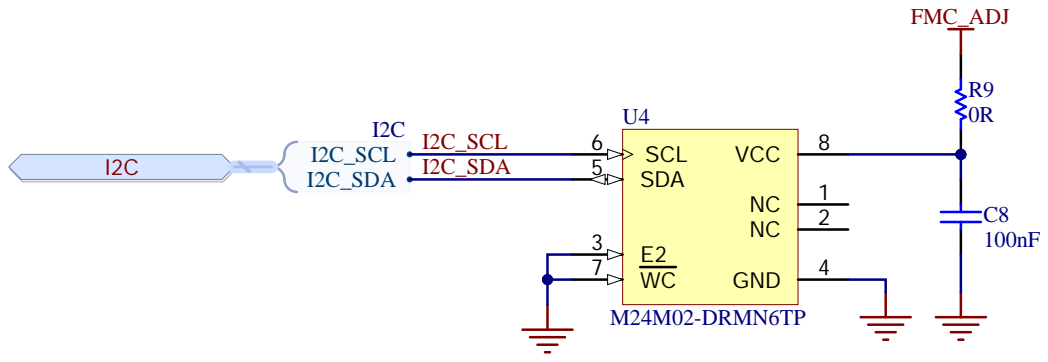
[picture p51: page 6]

Project: FPGA Pe rip h e rals Bo a rd - EEPR O M

Drawin g n umb er: Rev: PA | Forma t: A Q | L a b oratory: IIS | Sh eet: I2C_EEPROM.SchDo c

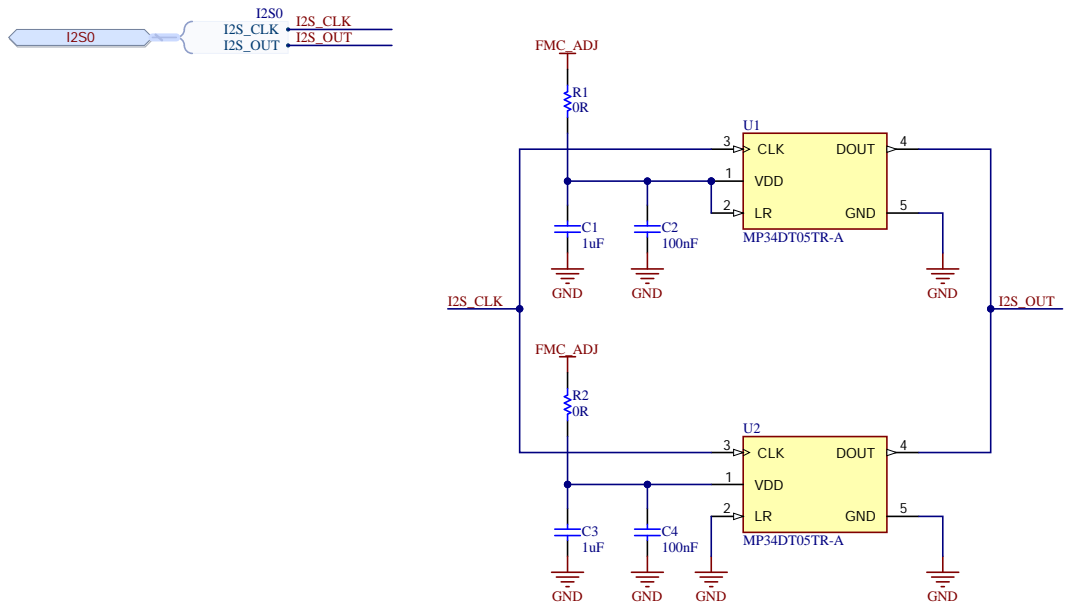
[picture p52: page 7]

Project: FPGA Pe rip h e rals Bo a rd - MIC

Drawin g n umb er: Rev: PA | Forma t: A Q | L a b oratory: IIS | Sh eet: I2S_Mic.Sch Doc
