pulp-platform/fmc_peripheral_boards/04_Expansion_Modules/Ethernet_Module/Documentation/ETH_Module_ASM.PDF

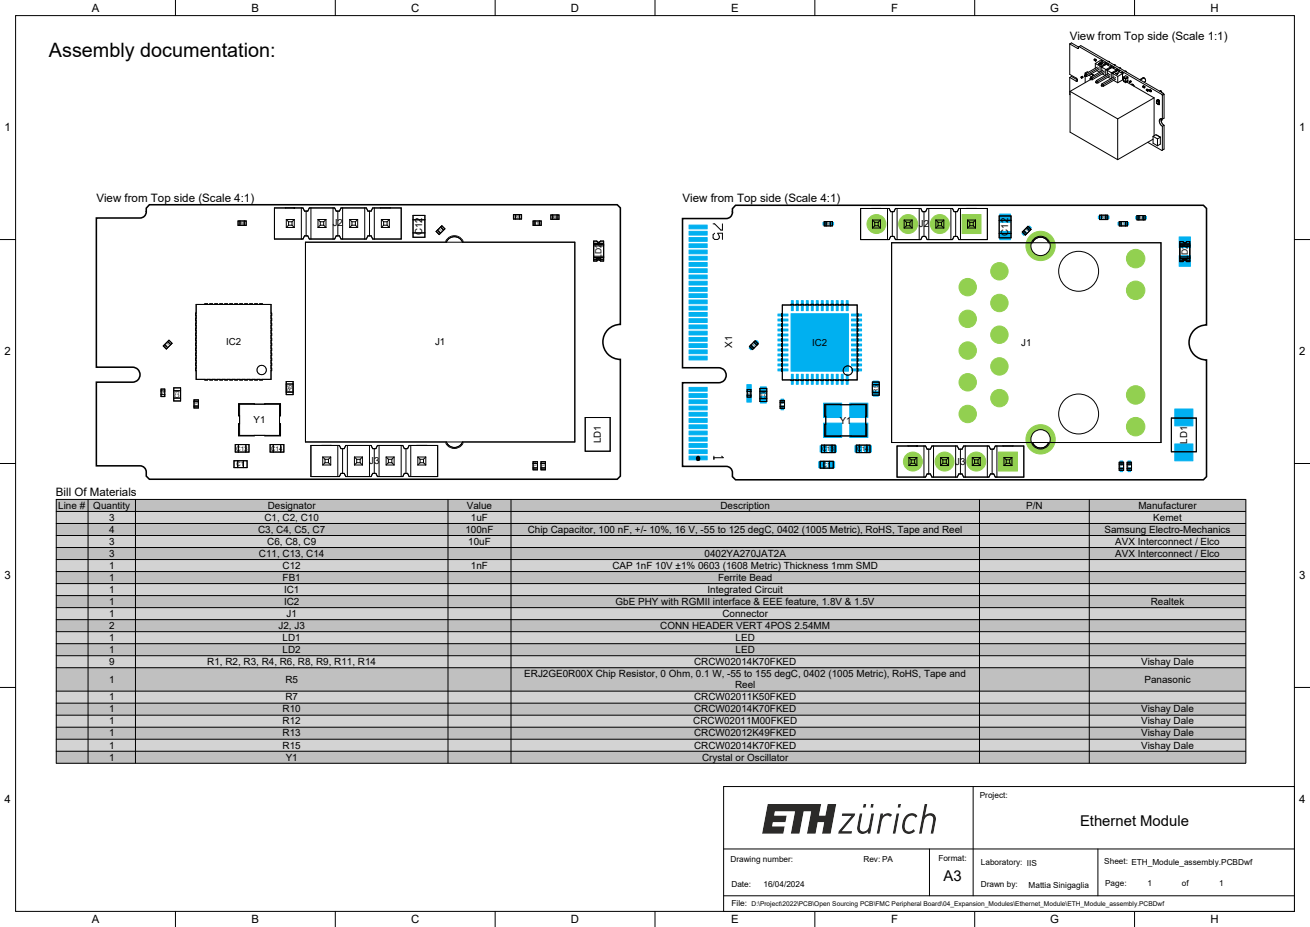
[picture p53: page 1]

View from Top side (Scale 1:1)

View from Top side (Scale 4:1)

Chip Capacitor, 100 nF, +/- 10%, 16 V, -55 to 125 degC, 0402 (1005 Metric), RoHS, Tape and Reel

CAP 1nF 10V ±1% 0603 (1608 Metric) Thickness 1mm SMD

GbE PHY with RGMII interface & EEE feature, 1.8V & 1.5V

ERJ2GE0R00X Chip Resistor, 0 Ohm, 0.1 W, -55 to 155 degC, 0402 (1005 Metric), RoHS, Tape and

File:
D:\Project\2022\PCB\Open Sourcing PCB\FMC Peripheral Board\04_Expansion_Modules\Ethernet_Module\ETH_Module_assembly.PCBDwf
