pulp-platform/fmc_peripheral_boards/04_Expansion_Modules/Ethernet_Module/Documentation/ETH_Module_FAB.PDF

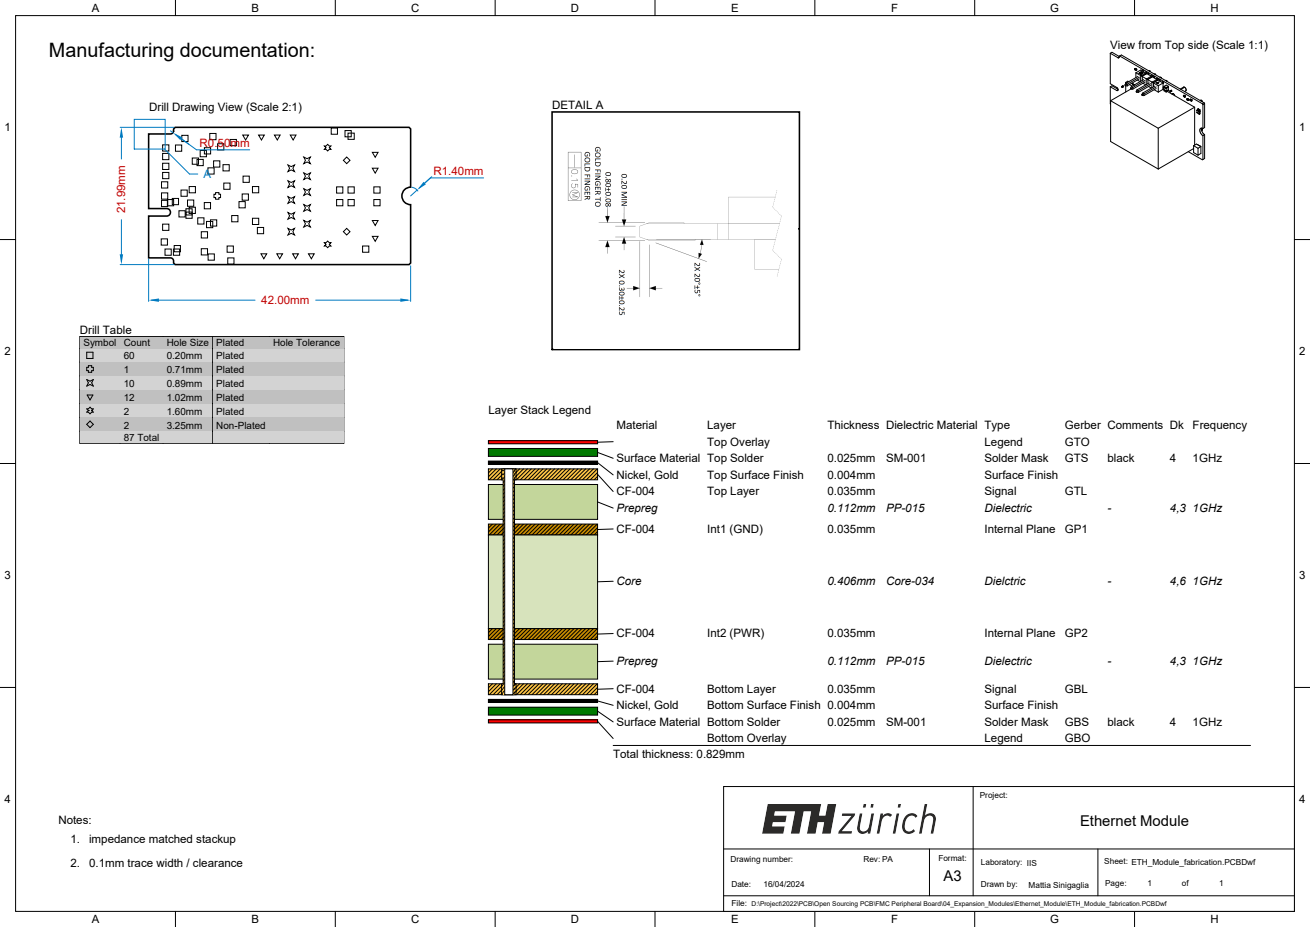
[picture p55: page 1]

View from Top side (Scale 1:1)

Drill Drawing View (Scale 2:1)

Symbol | Count | Hole Size | Plated | Hole Tolerance

60 | 0.20mm | Plated
1 | 0.71mm | Plated
10 | 0.89mm | Plated
12 | 1.02mm | Plated
2 | 1.60mm | Plated
2 | 3.25mm | Non-Plated
87 Total

Project: Ethernet Module

Drawing number: Rev: PA Date: 16/04/2024 | Format: | Laboratory: IIS Drawn by: Mattia Sinigaglia | Sheet: ETH_Module_fabrication.PCBDwf of A3 Page: 1 1

File:
D:\Project\2022\PCB\Open Sourcing PCB\FMC Peripheral Board\04_Expansion_Modules\Ethernet_Module\ETH_Module_fabrication.PCBDwf
