pulp-platform/fmc_peripheral_boards/04_Expansion_Modules/Ethernet_Module/Documentation/ETH_Module_LAY.PDF

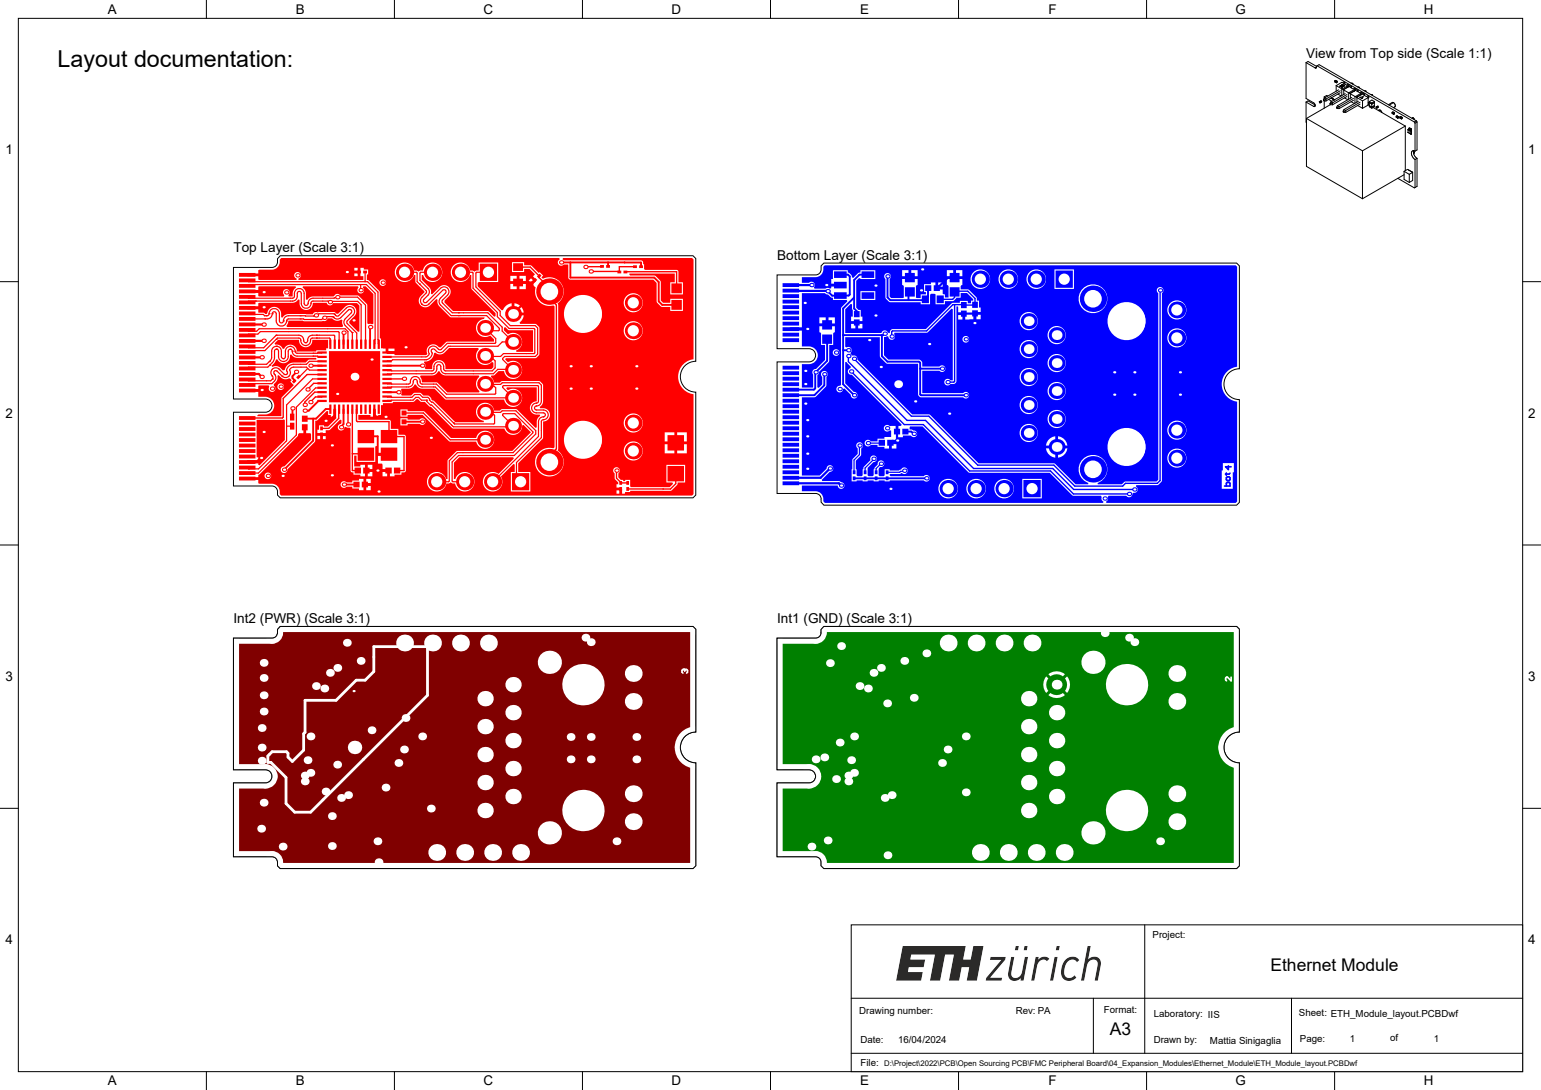
[picture p56: page 1]

View from Top side (Scale 1:1)

Project: Ethernet Module

Drawing number: Rev: PA Date: 16/04/2024 | Format: | Laboratory: IIS Drawn by: Mattia Sinigaglia | Sheet: ETH_Module_layout.PCBDwf of A3 Page: 1 1

File:
D:\Project\2022\PCB\Open Sourcing PCB\FMC Peripheral Board\04_Expansion_Modules\Ethernet_Module\ETH_Module_layout.PCBDwf
