pulp-platform/fmc_peripheral_boards/04_Expansion_Modules/Ethernet_Module/Documentation/ETH_Module_SCH.PDF

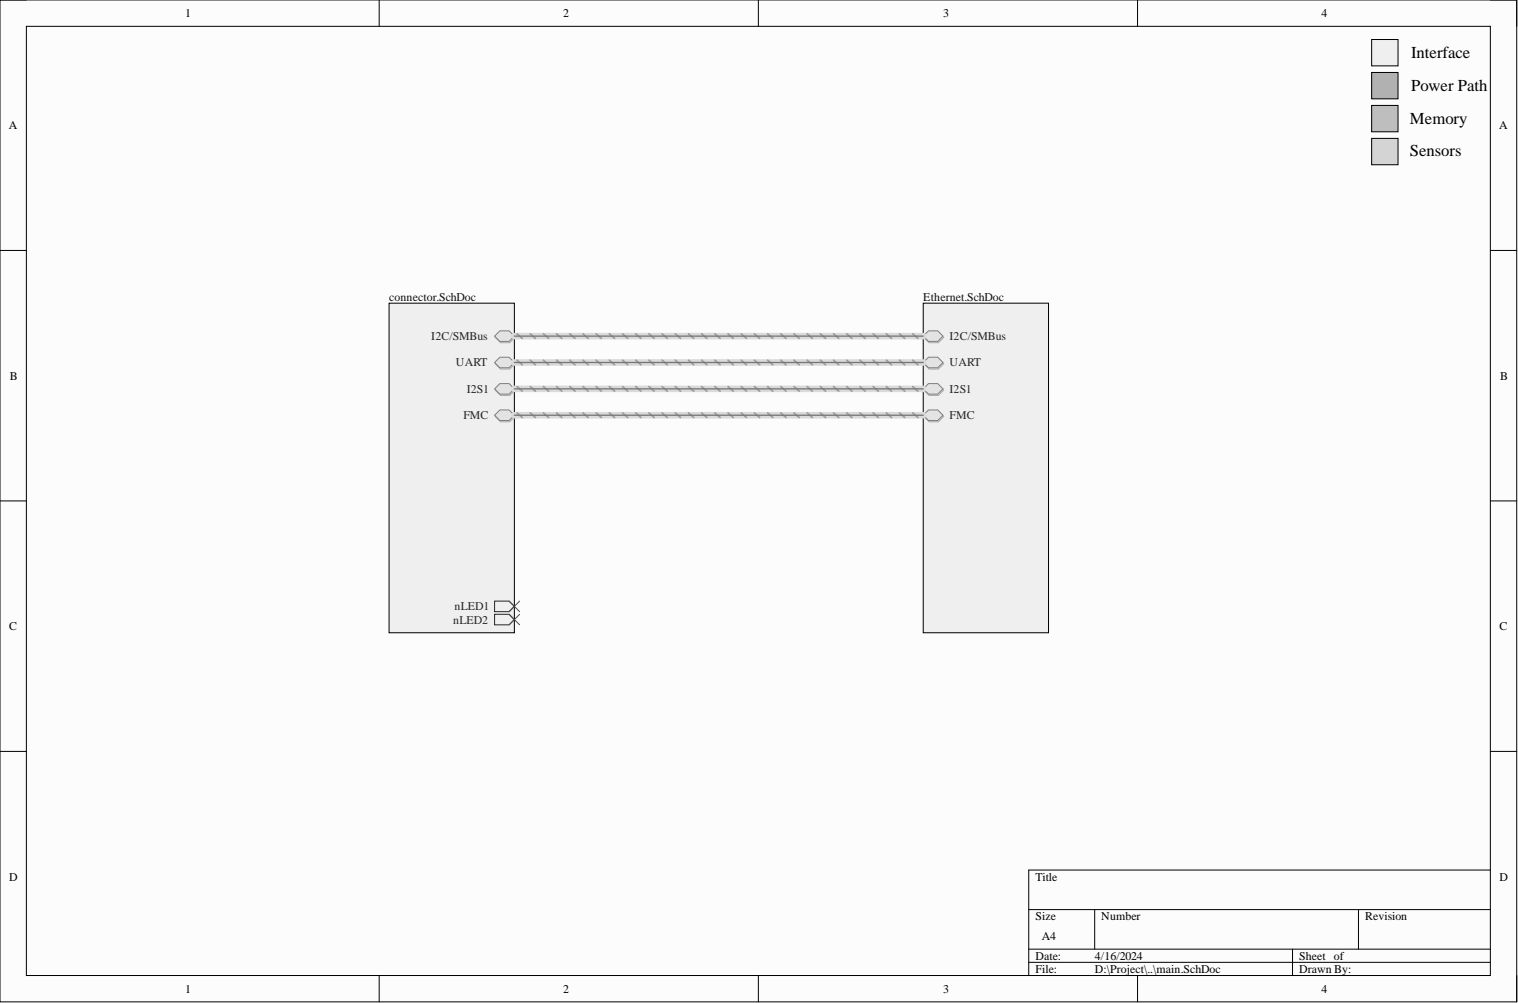
[picture p57: page 1]

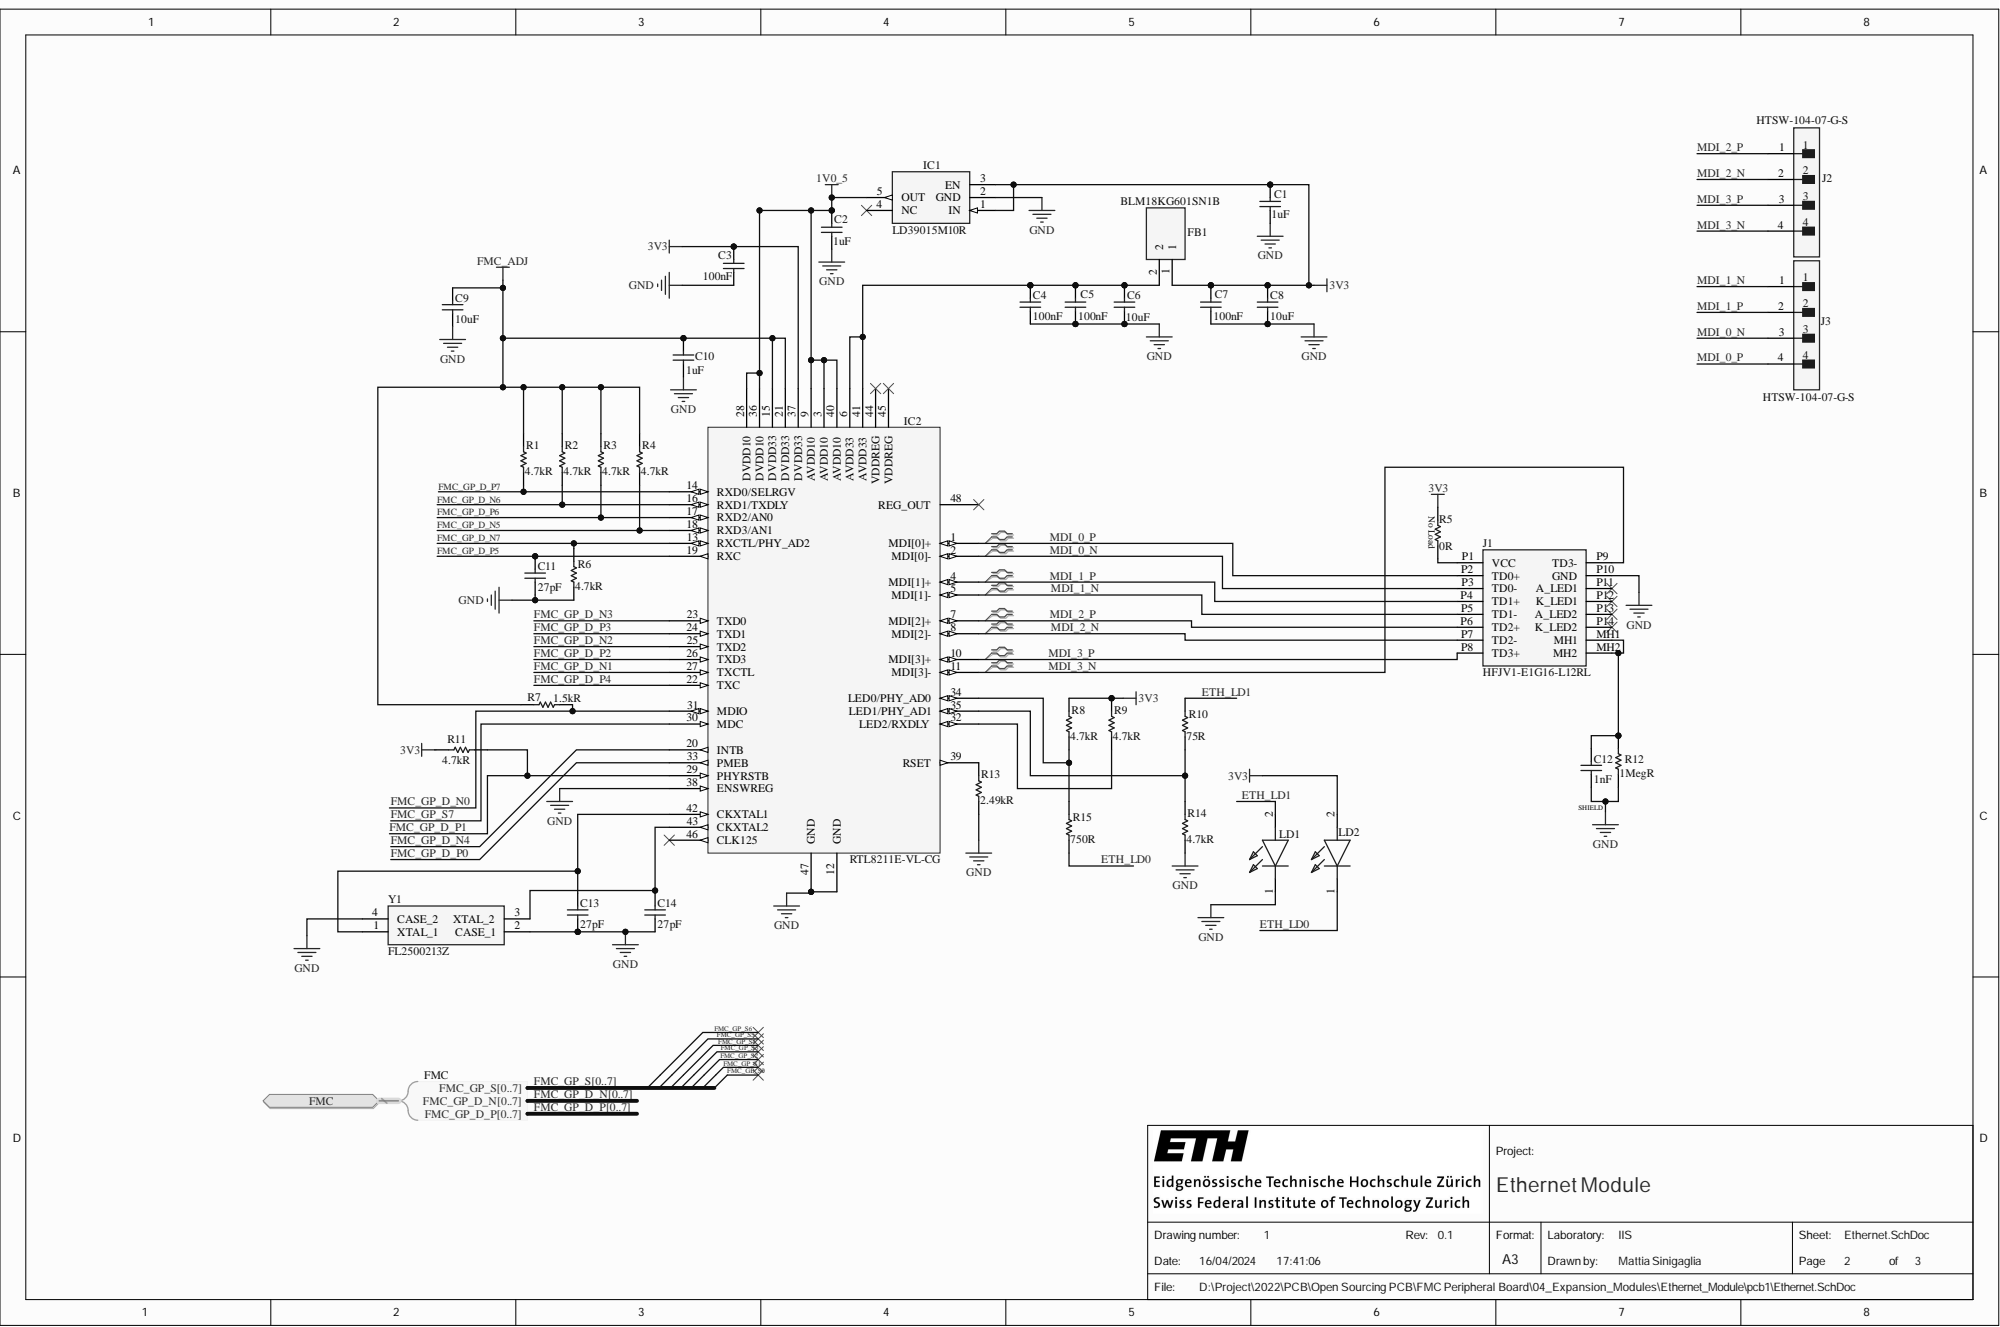
[picture p58: page 2]

2 | MDI_ 0 _N

4 | MDI_ 1 _P
5 | MDI_ 1 _N

4 2
4 3
4 6

FMC_ GP_S7
FMC_ GP_ D _ P 1

Proje c t: E th e r n e t M o d u l e

Drawing num b e r: R e v : 0. D a te : 16/04/202 17:41 : | Form a t: A | Laborato ry : I I S Drawn by : Mattia Sinigagl i a | Shee t: Ethernet. S c h D o c Pag e of

t\2022\PCB\Open Sourcing PCB\F

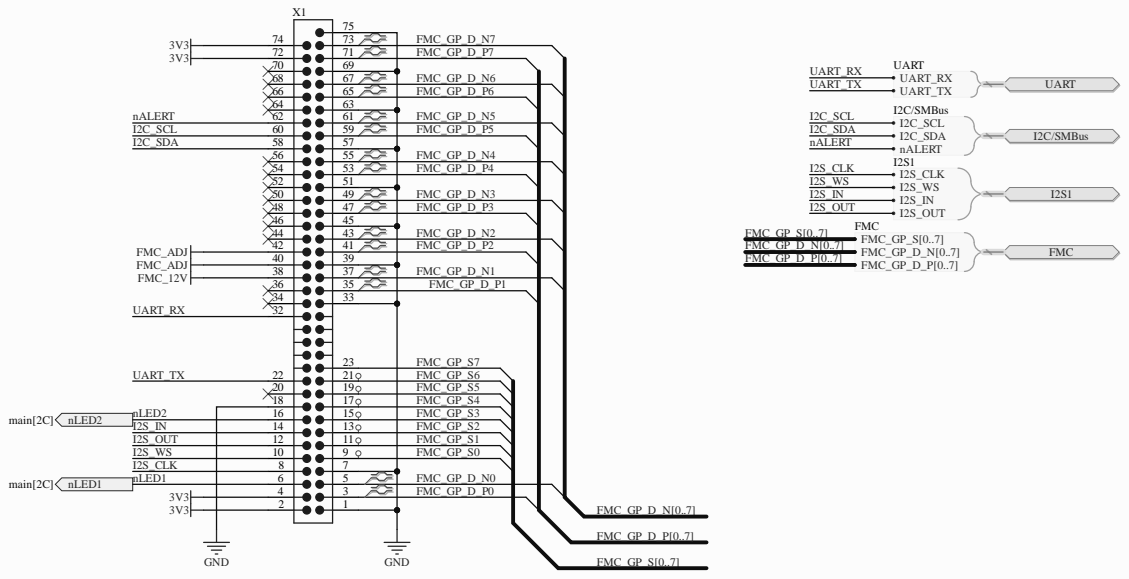
[picture p59: page 3]

Proje c t: E th e n e t M o d u l e

Drawing num b e r: R e v : 0. D a te : 16/04/202 17:41 : | Form a t: A | Laborato ry : I I S Drawn by : Mattia Sinigagl i a | Shee t: connec tor. S c h D o c Pag e of

t\2022\PCB\Open Sourcing PCB\F
