pulp-platform/fmc_peripheral_boards/04_Expansion_Modules/PWM_Module/Documentation/PWM_Module_ASM.PDF

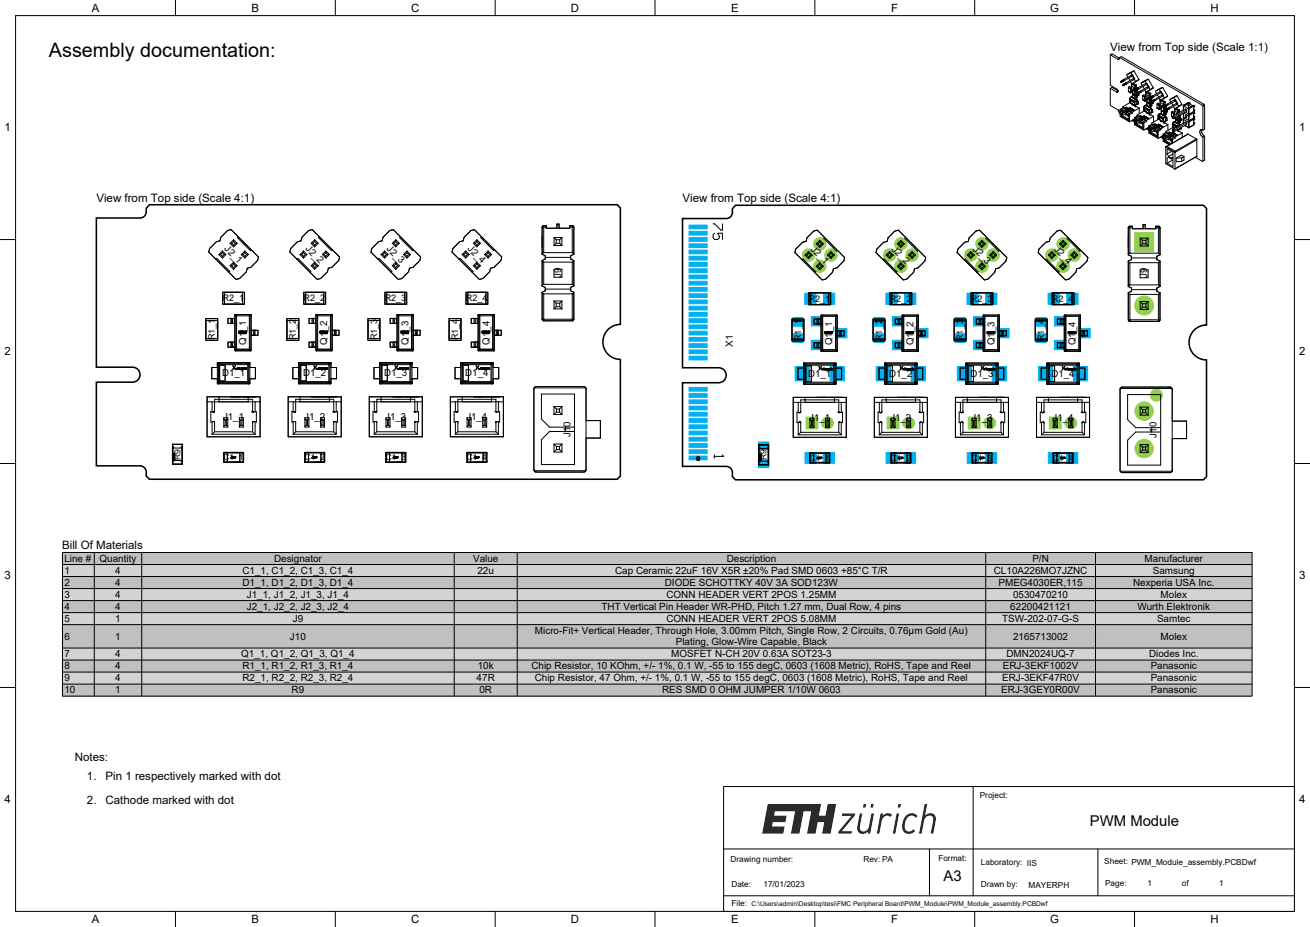
[picture p60: page 1]

View from Top side (Scale 1:1)

View from Top side (Scale 4:1)

Cap Ceramic 22uF 16V X5R ±20% Pad SMD 0603 +85°C T/R

THT Vertical Pin Header WR-PHD, Pitch 1.27 mm, Dual Row, 4 pins

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

Plating, Glow-Wire Capable, Black
MOSFET N-CH 20V 0.63A SOT23-3

Chip Resistor, 10 KOhm, +/- 1%, 0.1 W, -55 to 155 degC, 0603 (1608 Metric), RoHS, Tape and Reel
Chip Resistor, 47 Ohm, +/- 1%, 0.1 W, -55 to 155 degC, 0603 (1608 Metric), RoHS, Tape and Reel

RES SMD 0 OHM JUMPER 1/10W 0603

Notes:
1. Pin 1 respectively marked with dot

2. Cathode marked with dot

File:
C:\Users\admin\Desktop\tesi\FMC Peripheral Board\PWM_Module\PWM_Module_assembly.PCBDwf
