pulp-platform/fmc_peripheral_boards/04_Expansion_Modules/PWM_Module/Documentation/PWM_Module_CON.PDF

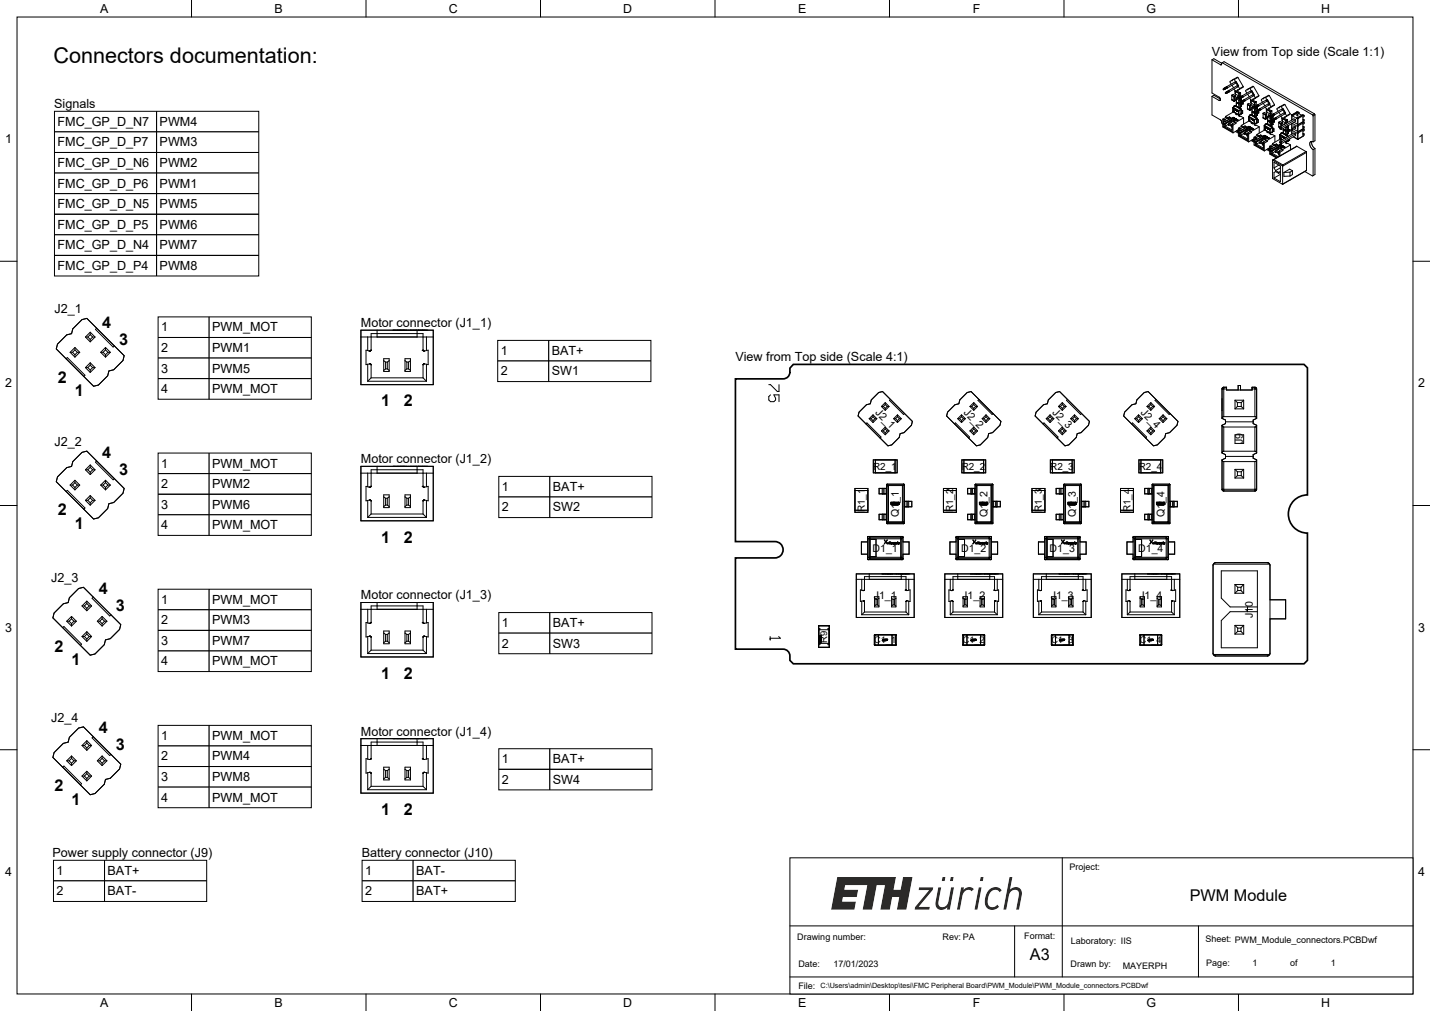
[picture p61: page 1]

View from Top side (Scale 1:1)

View from Top side (Scale 4:1)

File:
C:\Users\admin\Desktop\tesi\FMC Peripheral Board\PWM_Module\PWM_Module_connectors.PCBDwf
