pulp-platform/fmc_peripheral_boards/04_Expansion_Modules/PWM_Module/Documentation/PWM_Module_FAB.PDF

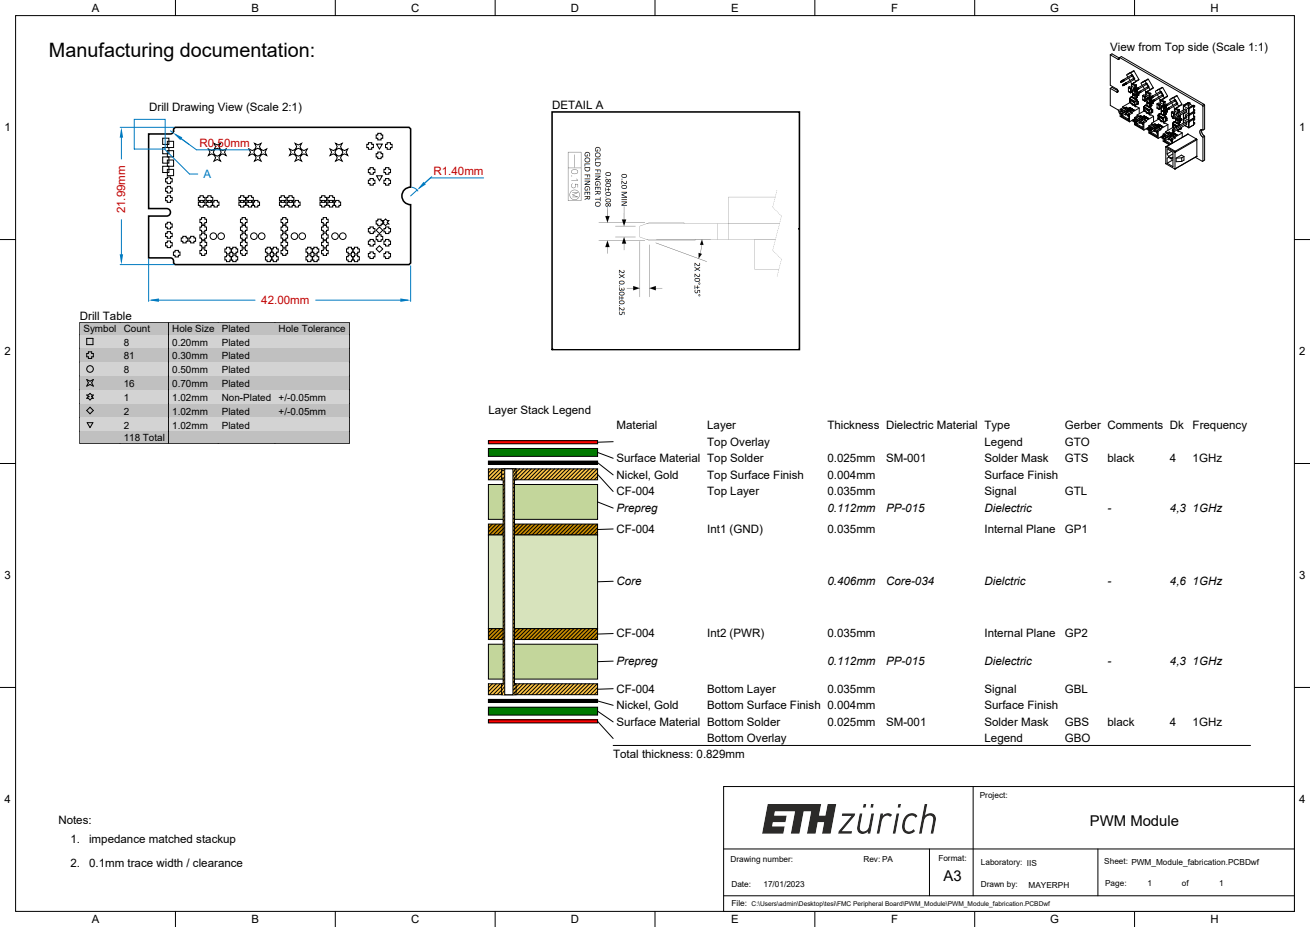
[picture p62: page 1]

View from Top side (Scale 1:1)

Drill Drawing View (Scale 2:1)

File:
C:\Users\admin\Desktop\tesi\FMC Peripheral Board\PWM_Module\PWM_Module_fabrication.PCBDwf
