pulp-platform/fmc_peripheral_boards/04_Expansion_Modules/PWM_Module/Documentation/PWM_Module_SCH.PDF

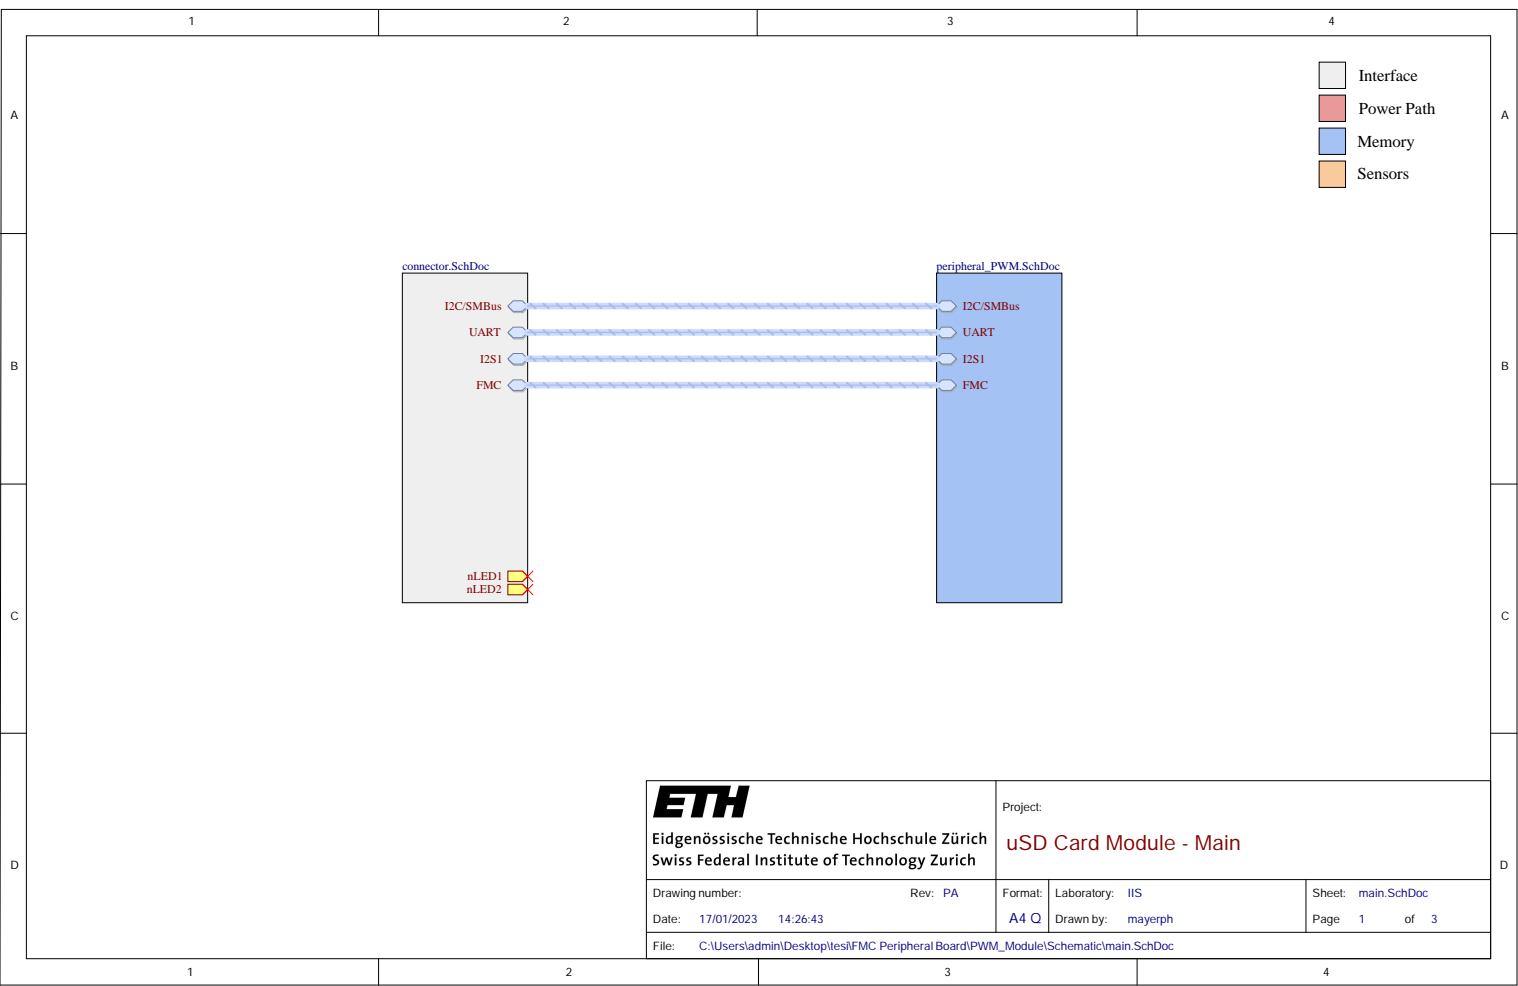
[picture p64: page 1]

Project: uSD Card Module - Main

Drawing number: Rev: PA Date: 14:26:43 | Format: A4 Q | Laboratory: IIS Drawn by: mayerph | Sheet: main.SchDoc Page 1 of 3

C:\Users\admin\Desktop\tesi\FMC Peripheral Board\PWM_Module\Schematic\main.SchDoc

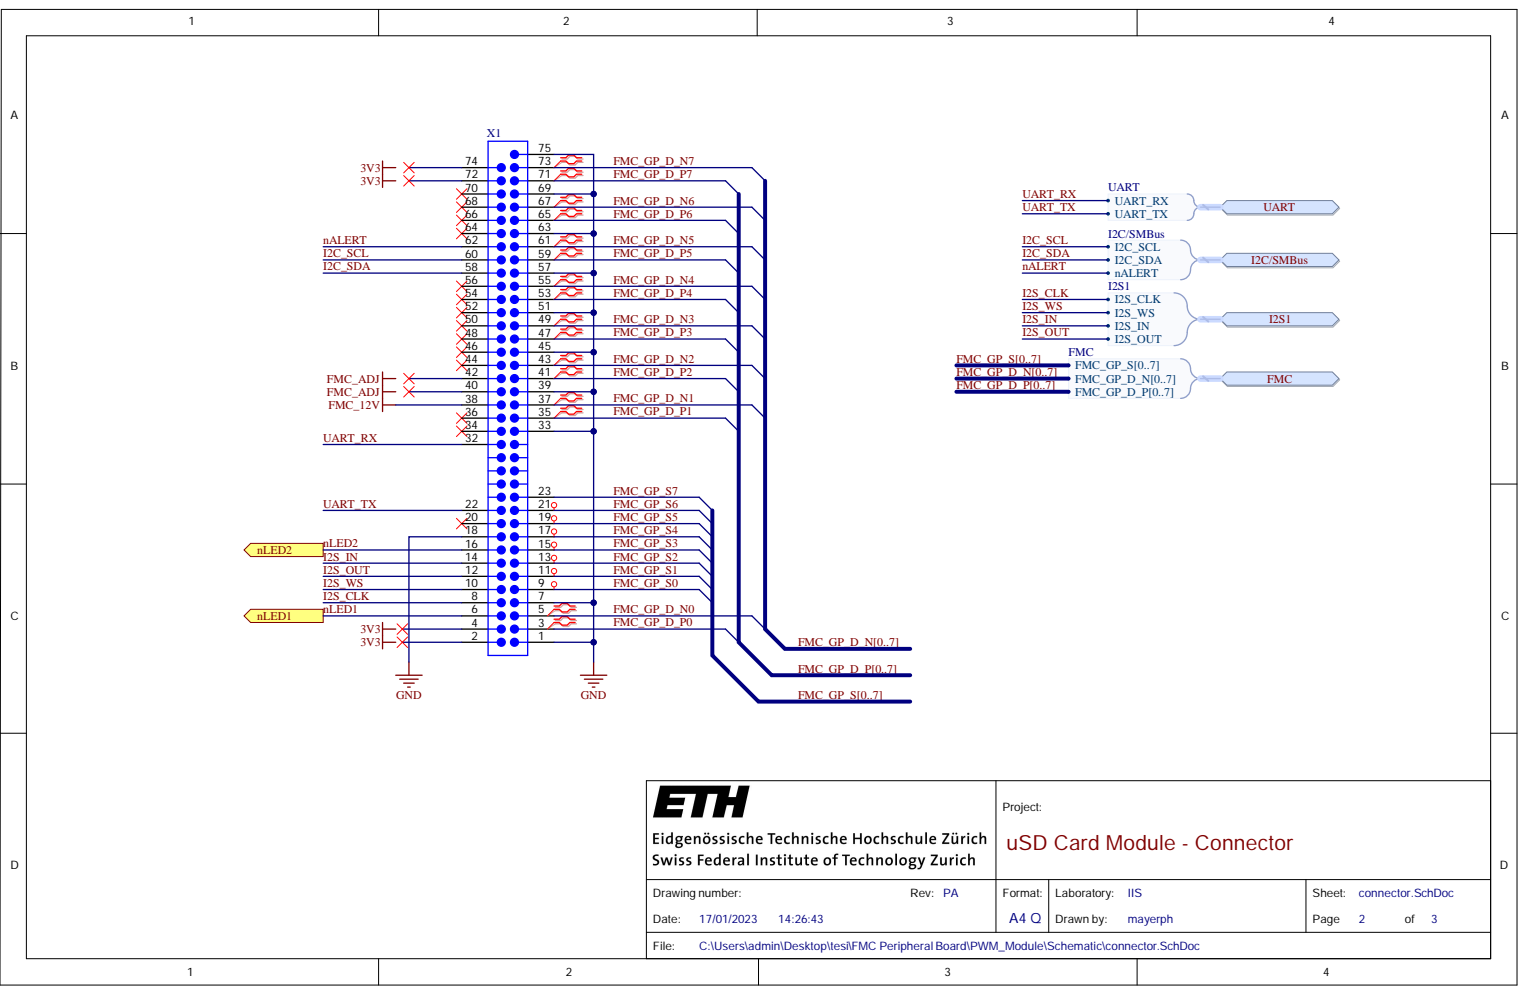
[picture p65: page 2]

Project: uSD C a rd Mo d ule - C o n n e cto r

Drawin g n umb er: Rev: PA 1 1 | Forma t: A 4 Q | L a b oratory: IIS Drawn by: | Sh eet: co n n ector. SchDoc Page 2 of 3

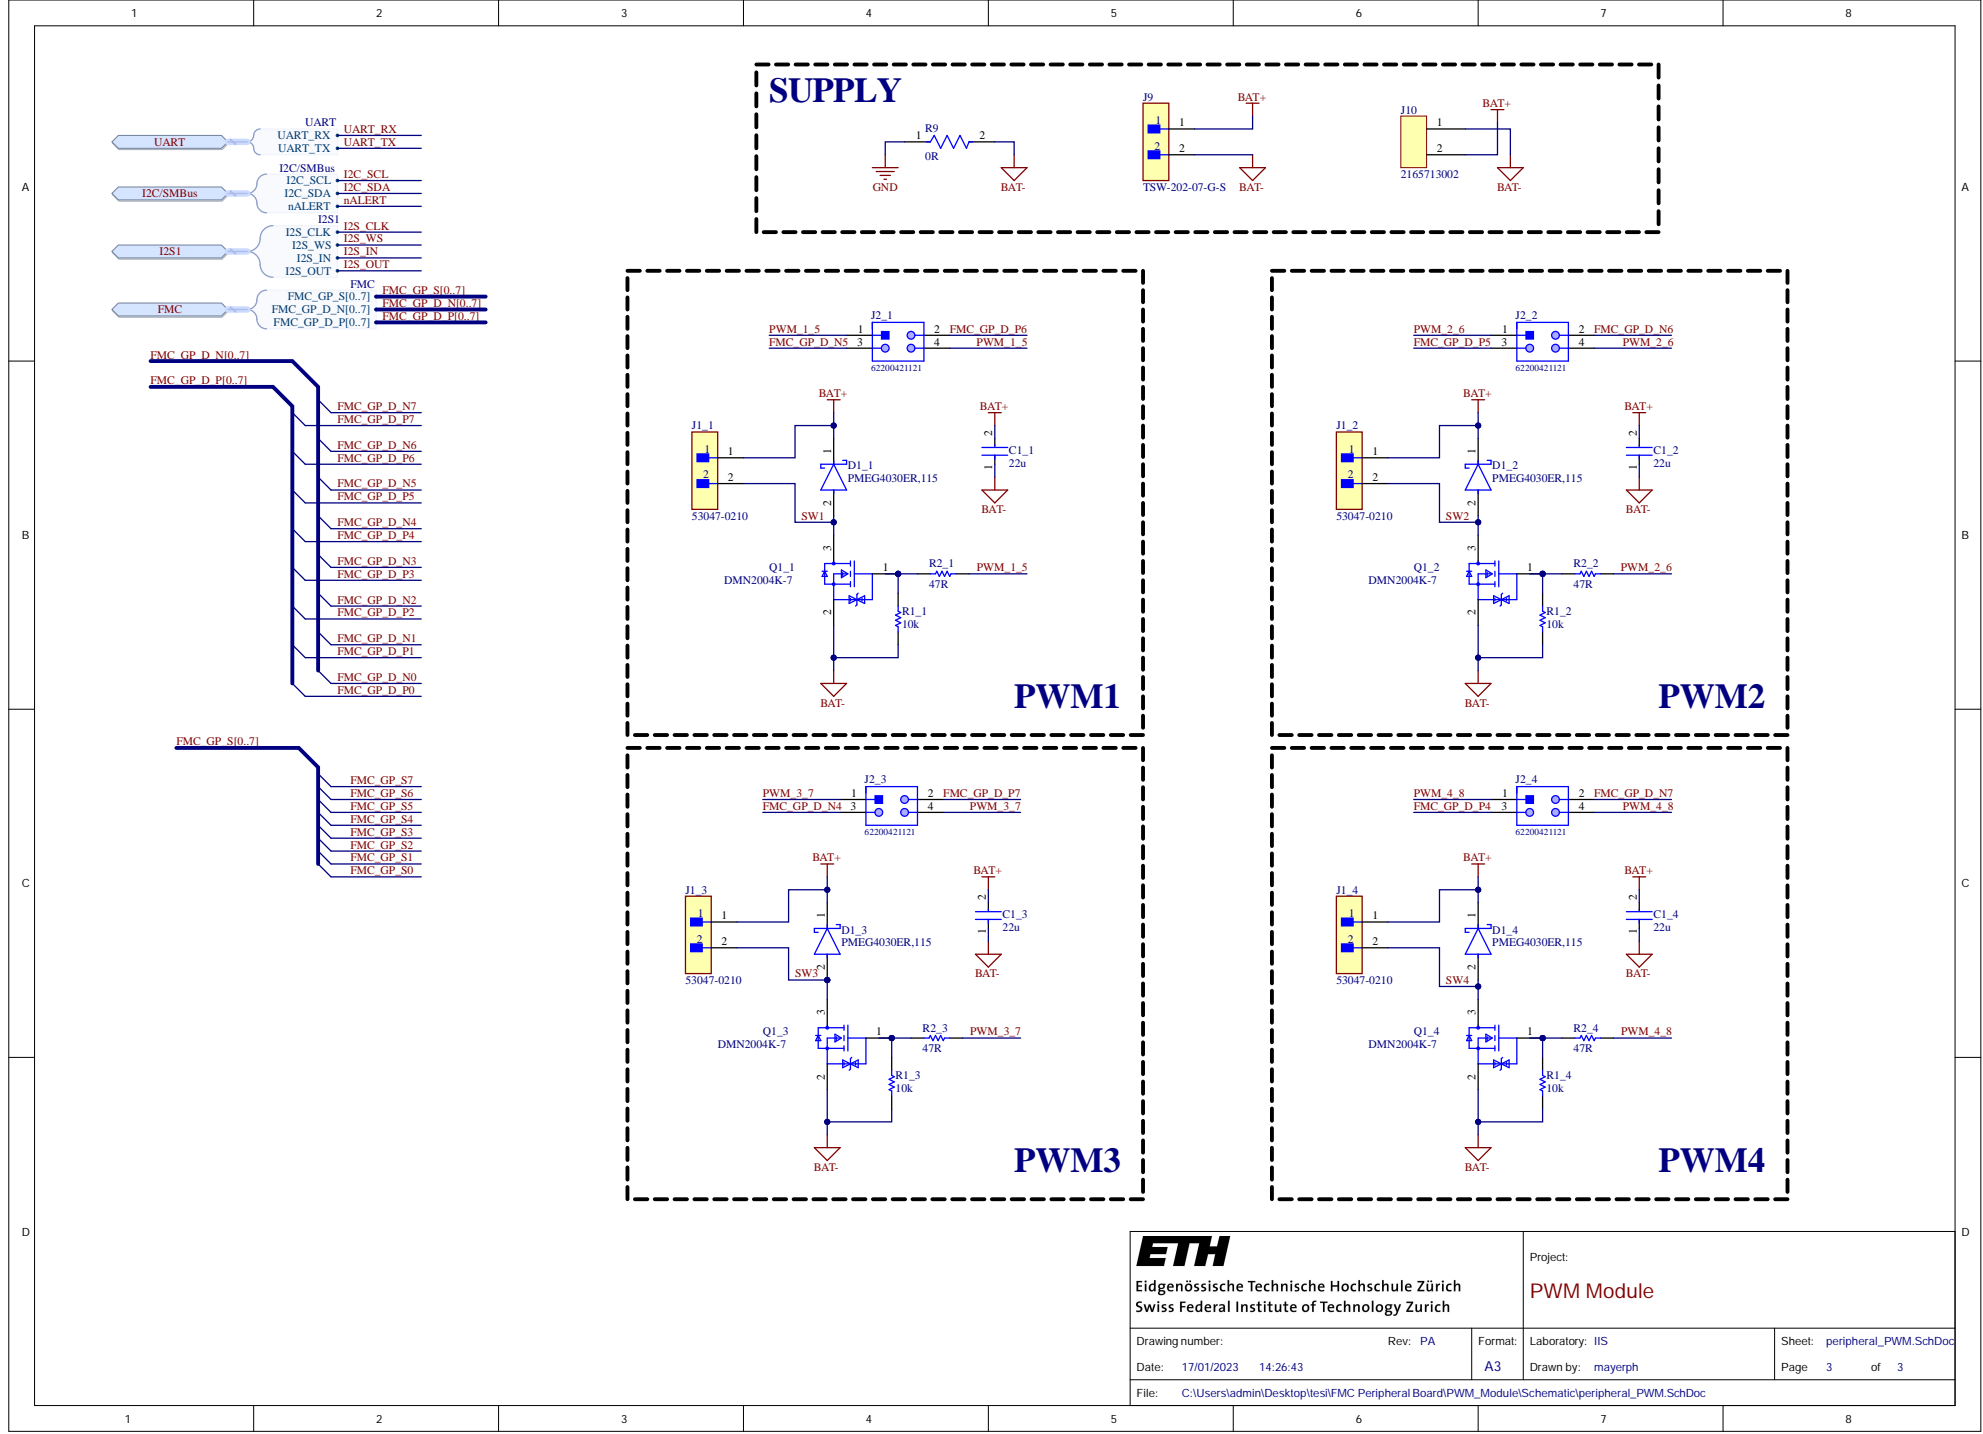
[picture p66: page 3]

Project: PWM Mo d ule

Drawin g n umb er: Rev: PA 1 1 | Forma t: A3 | L a b oratory: IIS Drawn by: | Sh eet: p erip h eral_PWM.SchDoc Page 3 of 3
