pulp-platform/fmc_peripheral_boards/04_Expansion_Modules/uSD_Module/Documentation/uSD_Module_CON.PDF

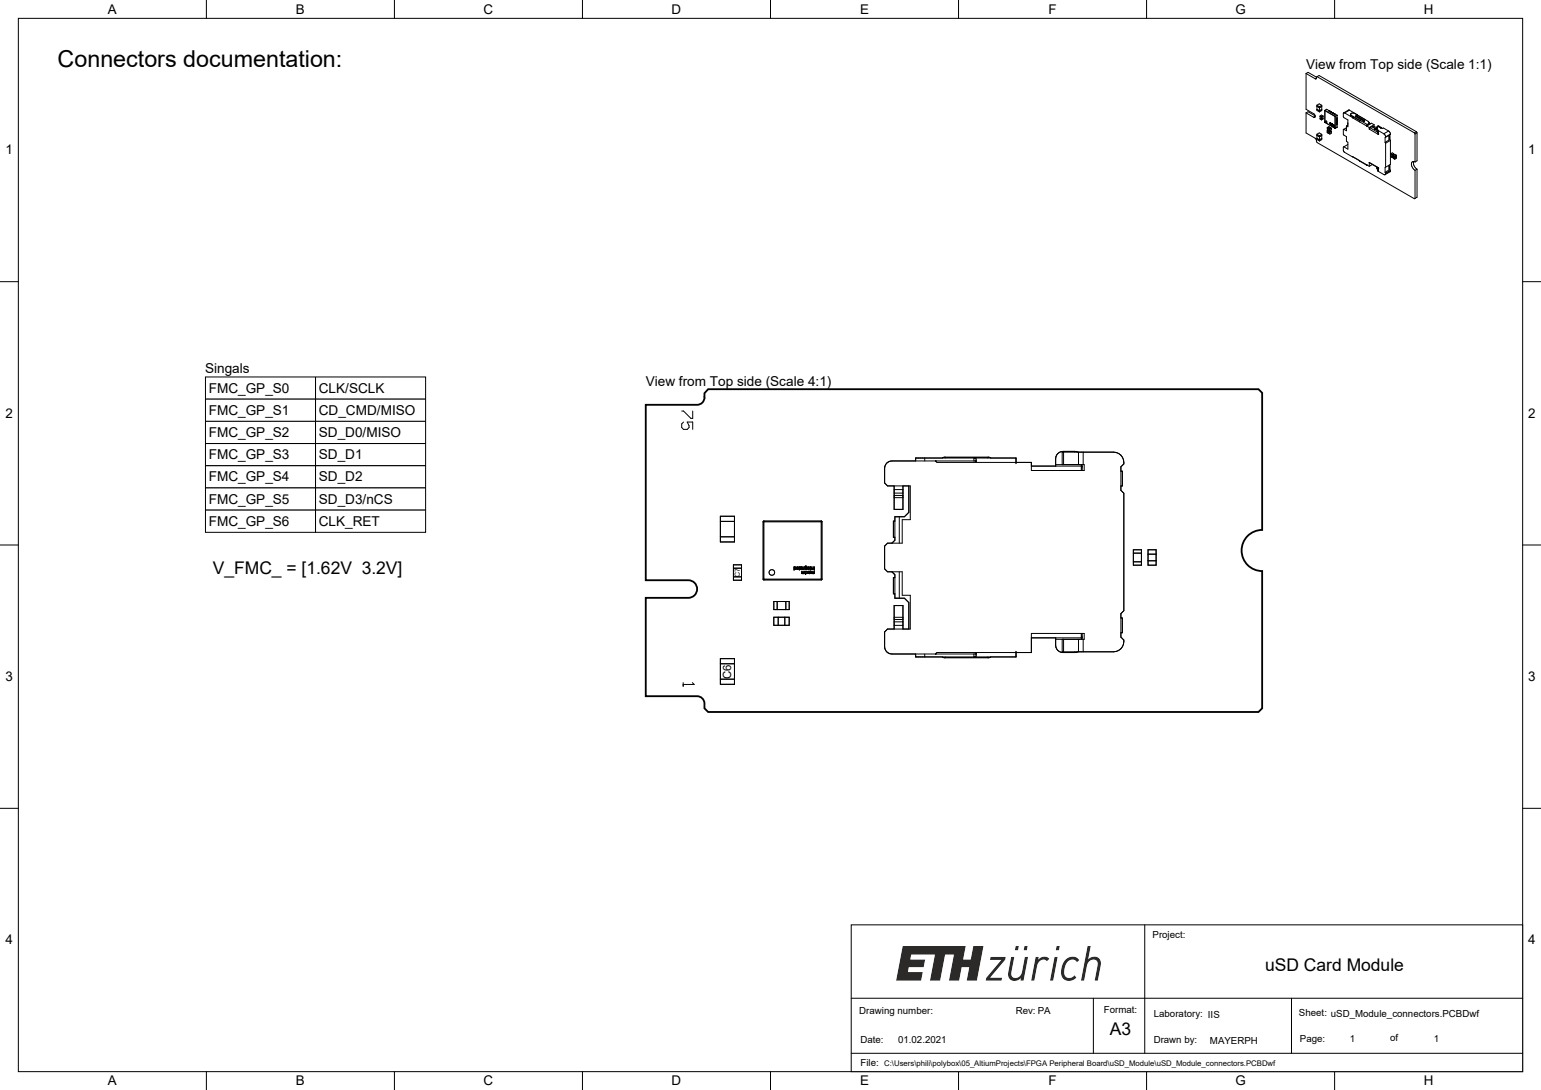
[picture p68: page 1]

View from Top side (Scale 1:1)

View from Top side (Scale 4:1)

FMC_GP_S0 | CLK/SCLK
FMC_GP_S1 | CD_CMD/MISO
FMC_GP_S2 | SD_D0/MISO
FMC_GP_S3 | SD_D1
FMC_GP_S4 | SD_D2
FMC_GP_S5 | SD_D3/nCS
FMC_GP_S6 | CLK_RET

Project: uSD Card Module

Drawing number: Rev: PA Date: 01.02.2021 | Format: | Laboratory: IIS Drawn by: MAYERPH | Sheet: uSD_Module_connectors.PCBDwf of A3 Page: 1 1

File:
C:\Users\phili\polybox\05_AltiumProjects\FPGA Peripheral Board\uSD_Module\uSD_Module_connectors.PCBDwf
