pulp-platform/fmc_peripheral_boards/04_Expansion_Modules/uSD_Module/Documentation/uSD_Module_FAB.PDF

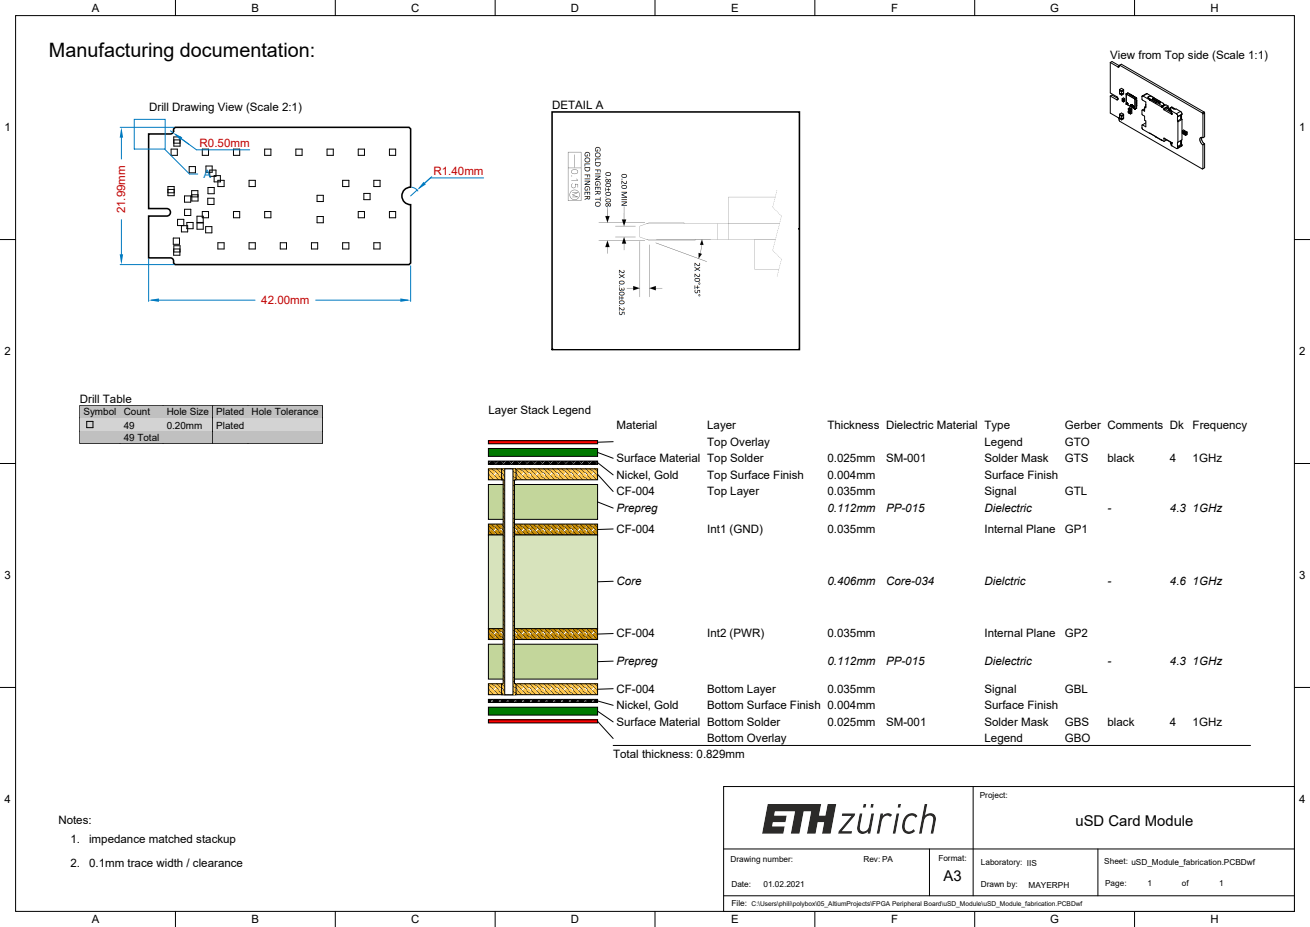
[picture p69: page 1]

View from Top side (Scale 1:1)

Drill Drawing View (Scale 2:1)

Symbol | Count | Hole Size | Plated | Hole Tolerance

49 | 0.20mm | Plated
49 Total

Project: uSD Card Module

Drawing number: Rev: PA Date: 01.02.2021 | Format: | Laboratory: IIS Drawn by: MAYERPH | Sheet: uSD_Module_fabrication.PCBDwf of A3 Page: 1 1

File:
C:\Users\phili\polybox\05_AltiumProjects\FPGA Peripheral Board\uSD_Module\uSD_Module_fabrication.PCBDwf
