pulp-platform/fmc_peripheral_boards/04_Expansion_Modules/uSD_Module/Documentation/uSD_Module_SCH.PDF

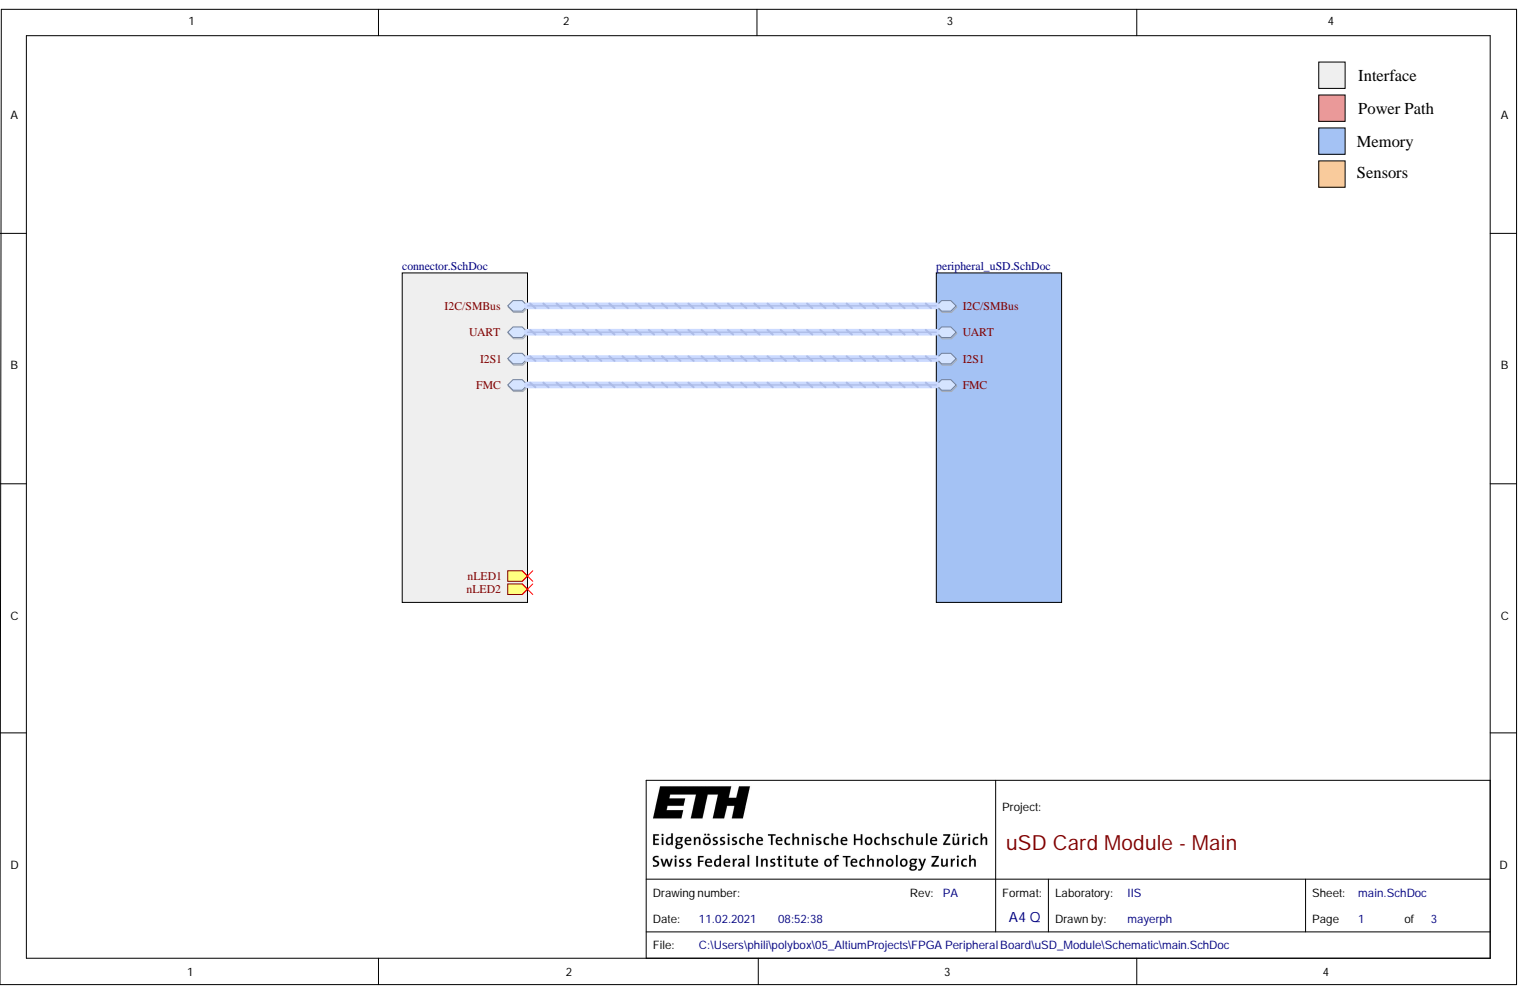
[picture p70: page 1]

Project: uSD Card Module - Main

Drawing number: Rev: PA Date: 11.02.2021 08:52:38 | Format: A4 Q | Laboratory: IIS Drawn by: mayerph | Sheet: main.SchDoc Page 1 of 3

C:\Users\phili\polybox\05_AltiumProjects\FPGA Peripheral Board\uSD_Module\Schematic\main.SchDoc

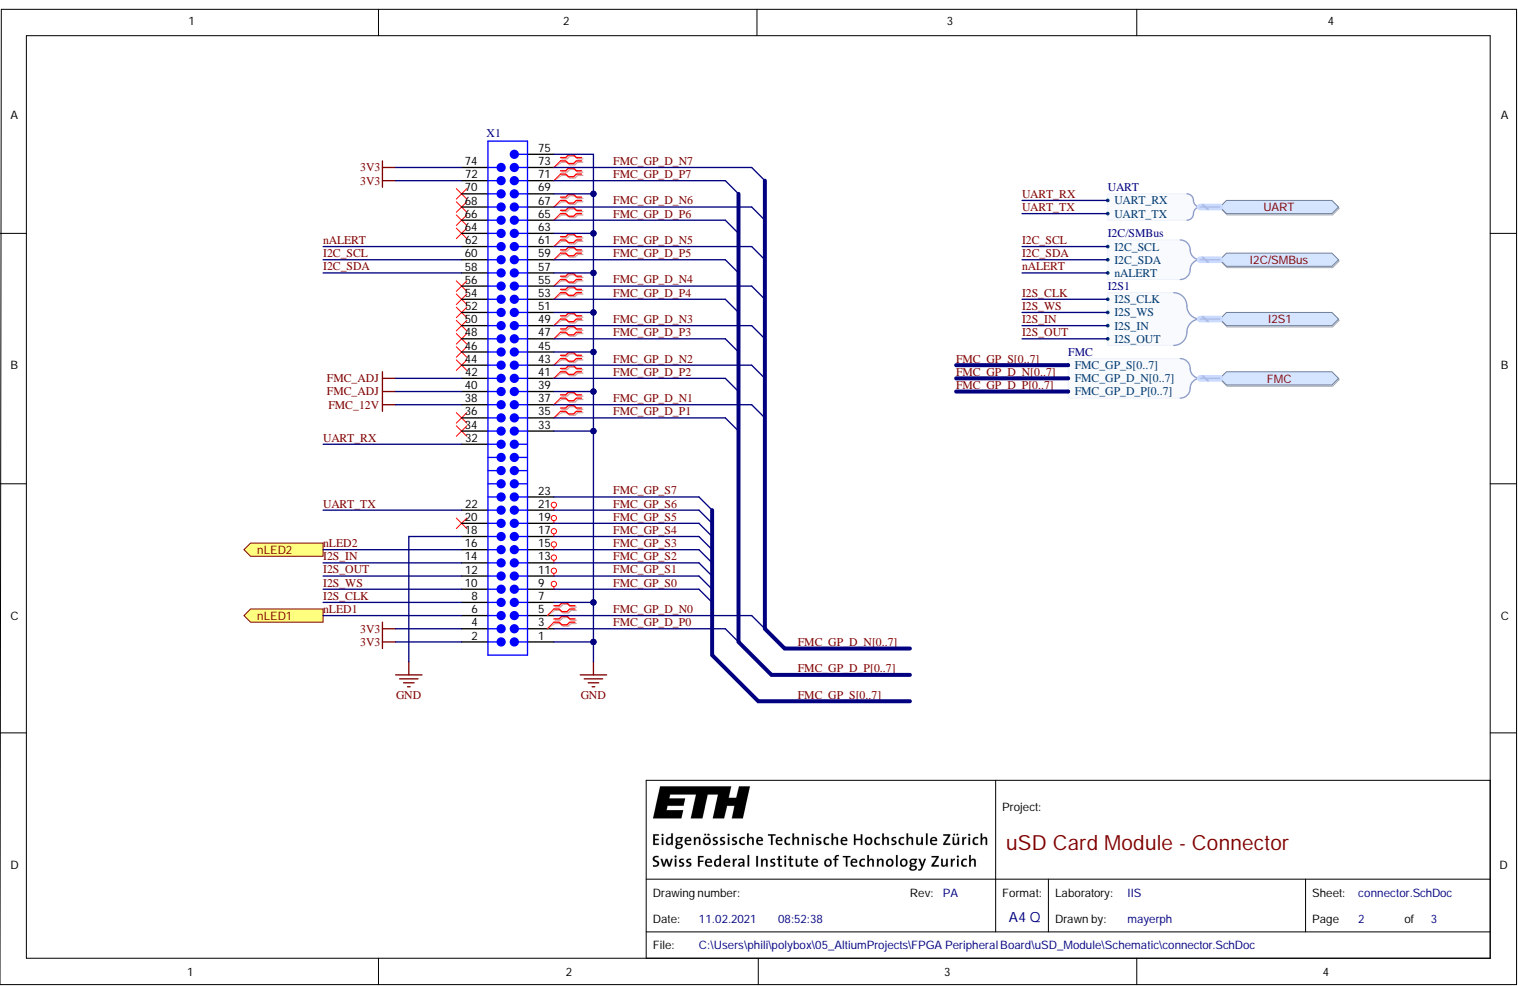
[picture p71: page 2]

Project: uSD C a rd Mo d ule - C o n n e cto r

Drawin g n umb er: Rev: PA 1 0 | Forma t: A 4 Q | L a b oratory: IIS Drawn by: | Sh eet: co n n ector. SchDoc Page 2 of 3

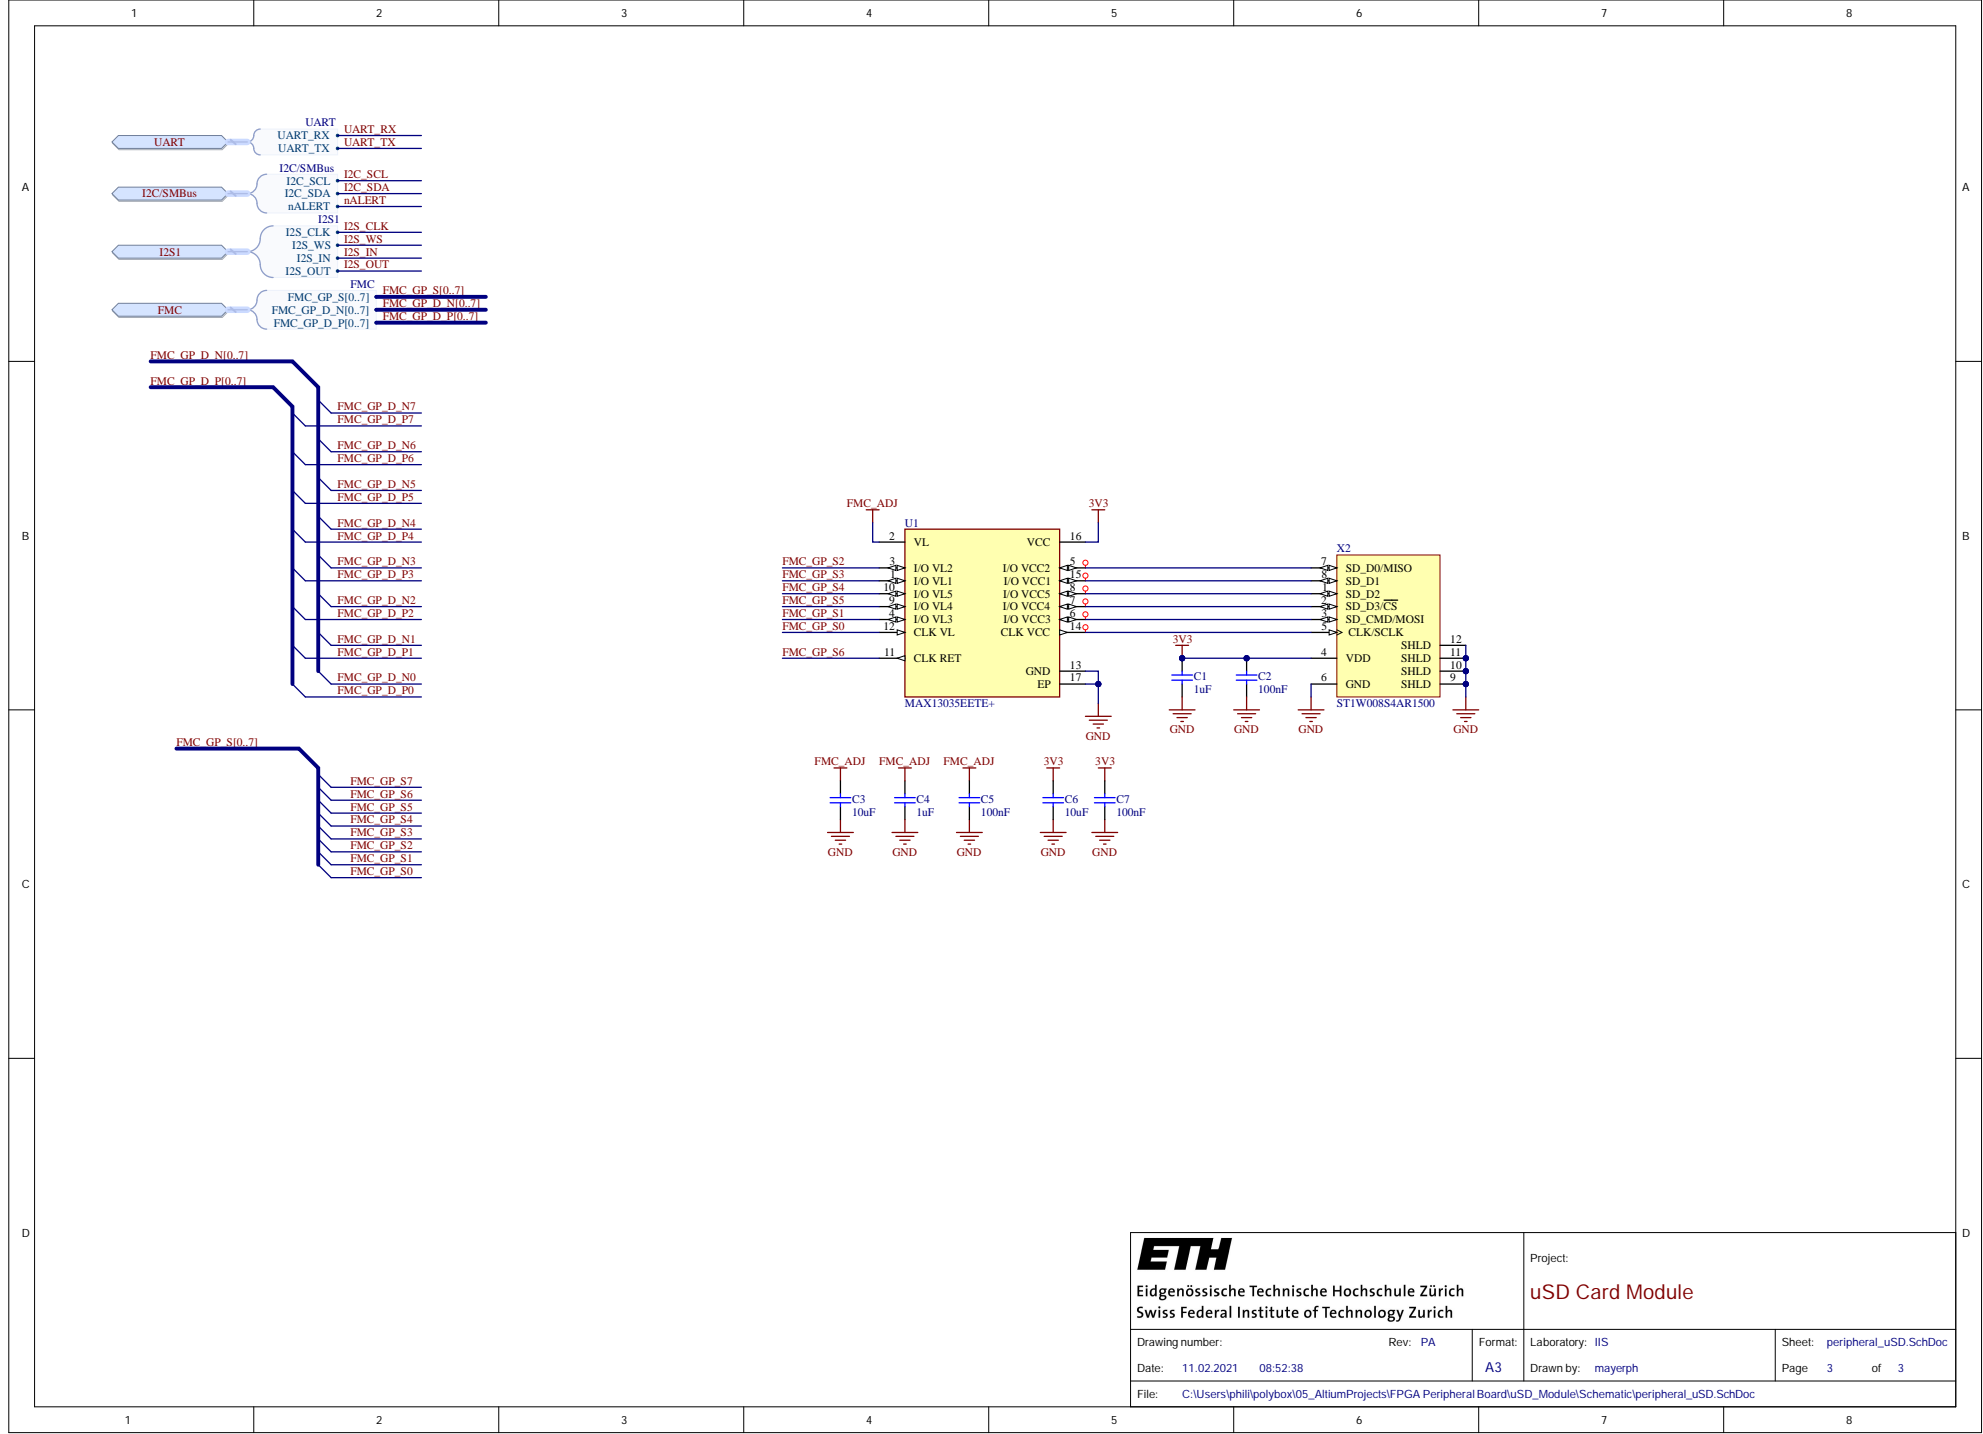
[picture p72: page 3]

Project: uSD C a rd Mo d ule

Drawin g n umb er: Rev: PA 1 0 | Forma t: A3 | L a b oratory: IIS Drawn by: | Sh eet: p erip h eral_uSD.SchDoc Page 3 of 3
