pulp-platform/fmc_peripheral_boards/04_Expansion_Modules/USART_Module/hw/Documentation/UART_Module_ASM.PDF

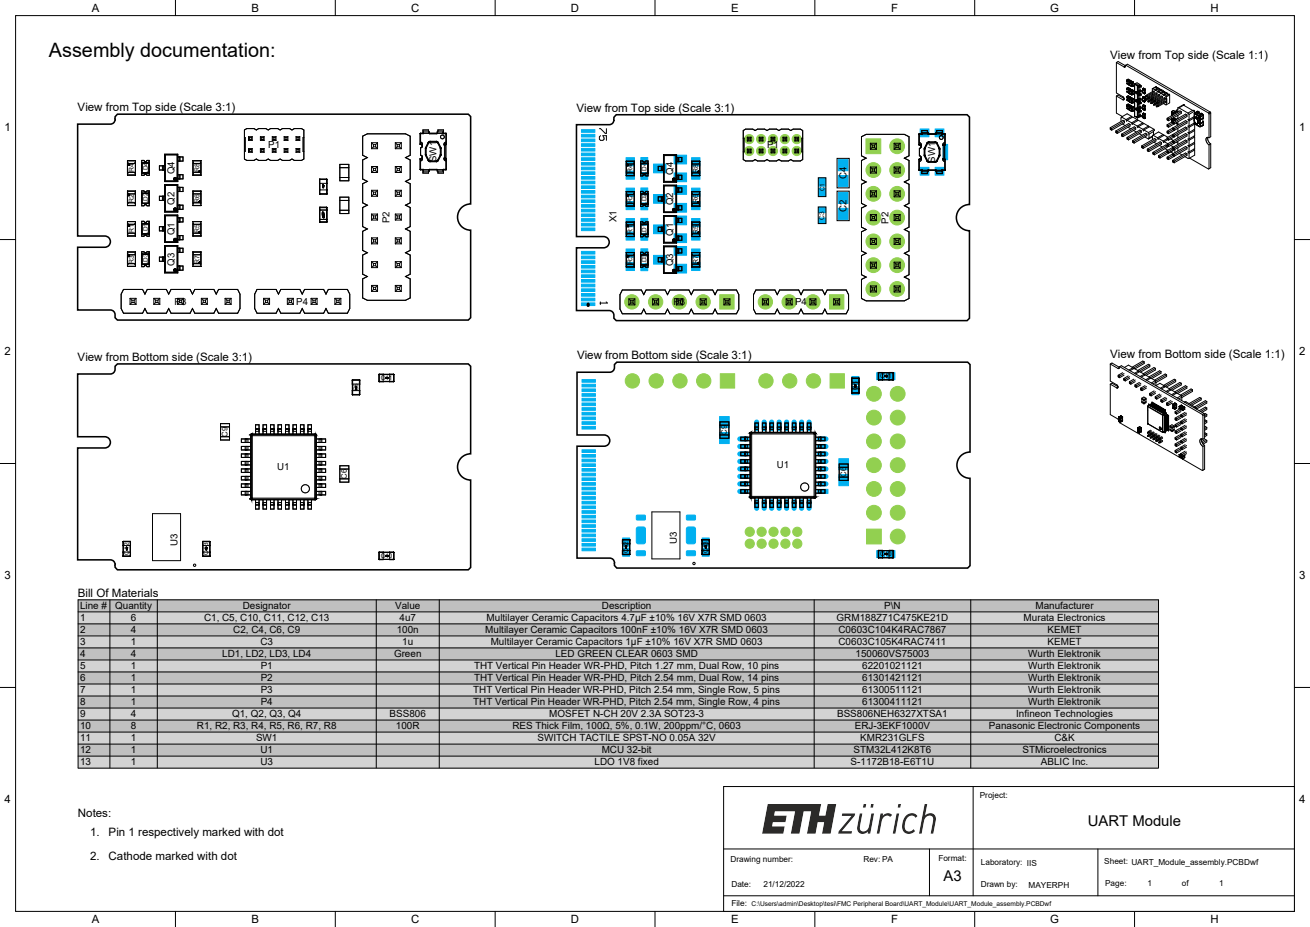
[picture p73: page 1]

View from Top side (Scale 1:1)

View from Top side (Scale 3:1)

View from Bottom side (Scale 3:1)

Multilayer Ceramic Capacitors 4.7μF ±10% 16V X7R SMD 0603
Multilayer Ceramic Capacitors 100nF ±10% 16V X7R SMD 0603
Multilayer Ceramic Capacitors 1μF ±10% 16V X7R SMD 0603

LED GREEN CLEAR 0603 SMD

THT Vertical Pin Header WR-PHD, Pitch 1.27 mm, Dual Row, 10 pins
THT Vertical Pin Header WR-PHD, Pitch 2.54 mm, Dual Row, 14 pins
THT Vertical Pin Header WR-PHD, Pitch 2.54 mm, Single Row, 5 pins
THT Vertical Pin Header WR-PHD, Pitch 2.54 mm, Single Row, 4 pins

RES Thick Film, 100Ω, 5%, 0.1W, 200ppm/°C, 0603
SWITCH TACTILE SPST-NO 0.05A 32V

Notes:
1. Pin 1 respectively marked with dot

2. Cathode marked with dot

File:
C:\Users\admin\Desktop\tesi\FMC Peripheral Board\UART_Module\UART_Module_assembly.PCBDwf
