pulp-platform/fmc_peripheral_boards/04_Expansion_Modules/USART_Module/hw/Documentation/UART_Module_CON.PDF

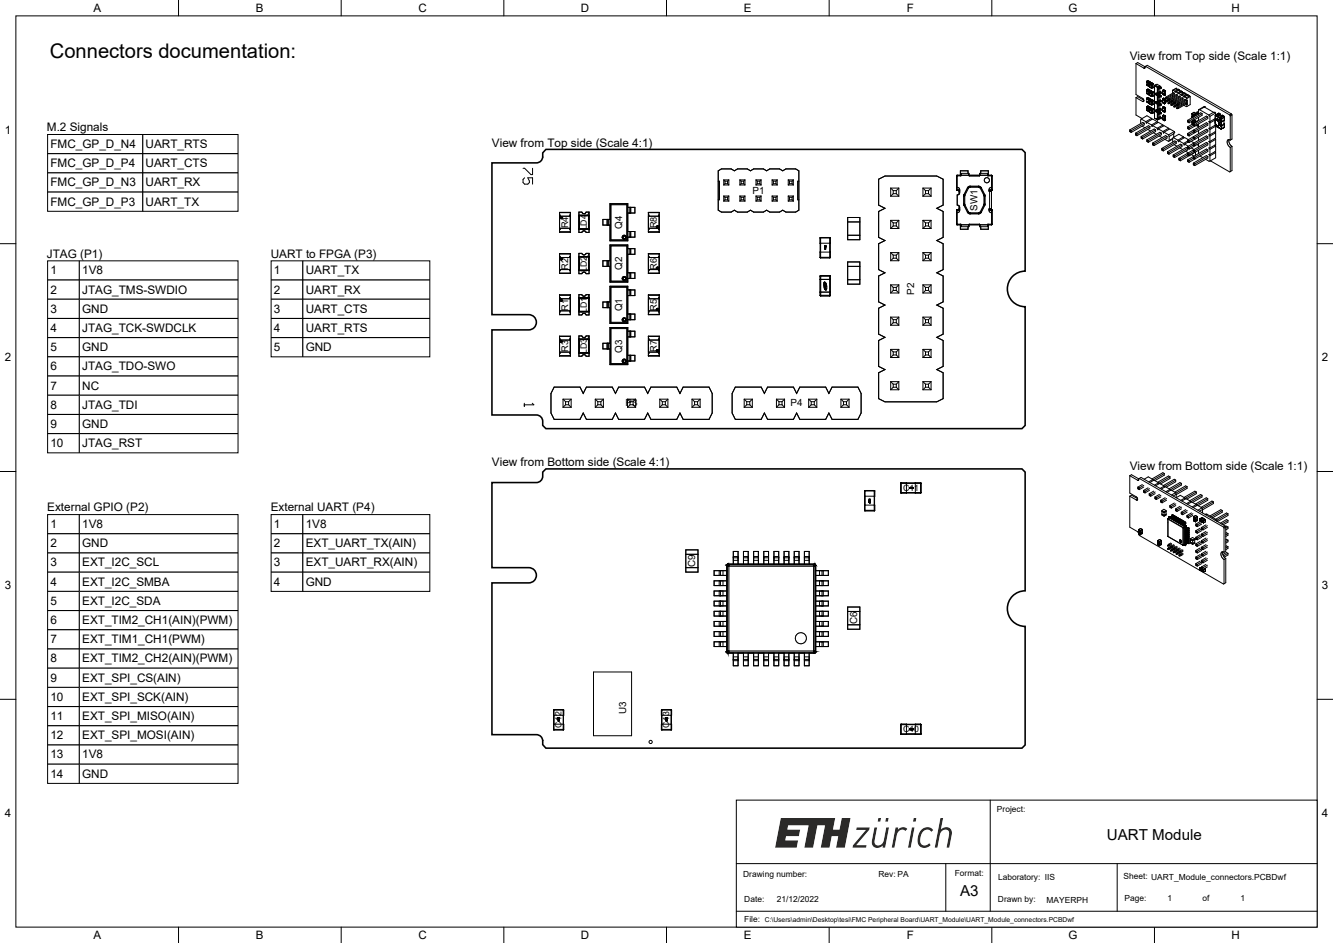
[picture p74: page 1]

Connectors documentation:
View from Top side (Scale 4:1) U3

View from Top side (Scale 1:1)

File:
C:\Users\admin\Desktop\tesi\FMC Peripheral Board\UART_Module\UART_Module_connectors.PCBDwf
