pulp-platform/fmc_peripheral_boards/04_Expansion_Modules/USART_Module/hw/Documentation/UART_Module_LAY.PDF

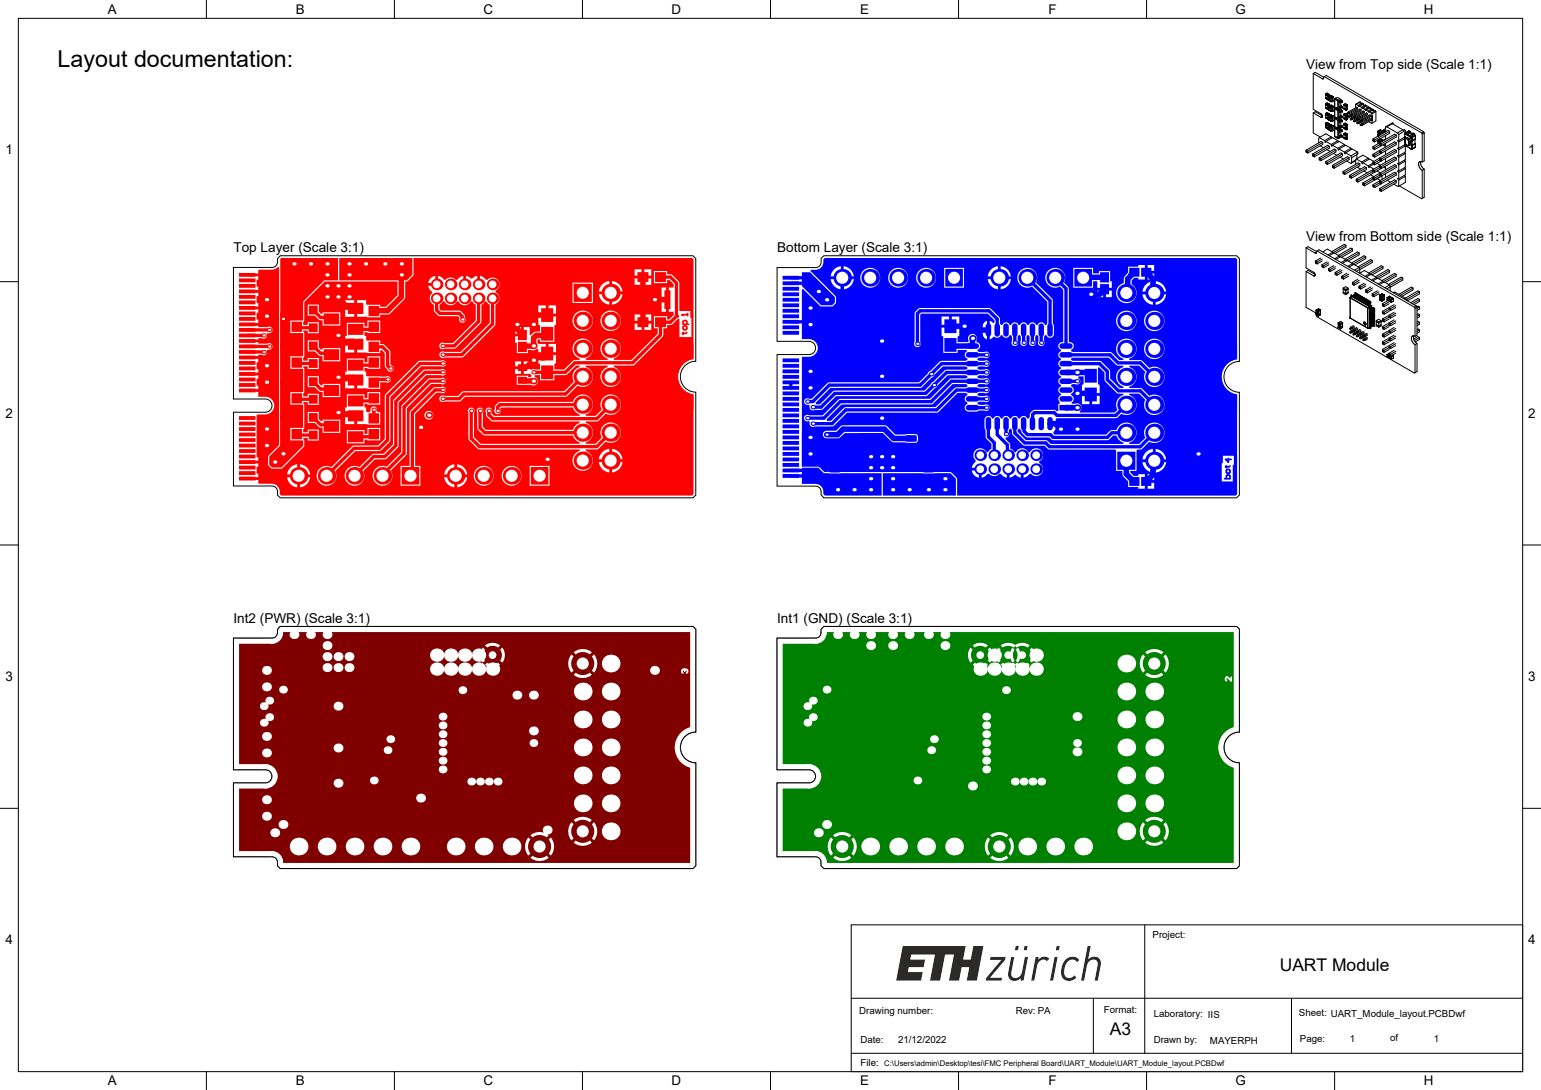
[picture p76: page 1]

View from Top side (Scale 1:1)

View from Bottom side (Scale 1:1)

File:
C:\Users\admin\Desktop\tesi\FMC Peripheral Board\UART_Module\UART_Module_layout.PCBDwf
