pulp-platform/fmc_peripheral_boards/04_Expansion_Modules/USART_Module/hw/Documentation/UART_Module_SCH.PDF

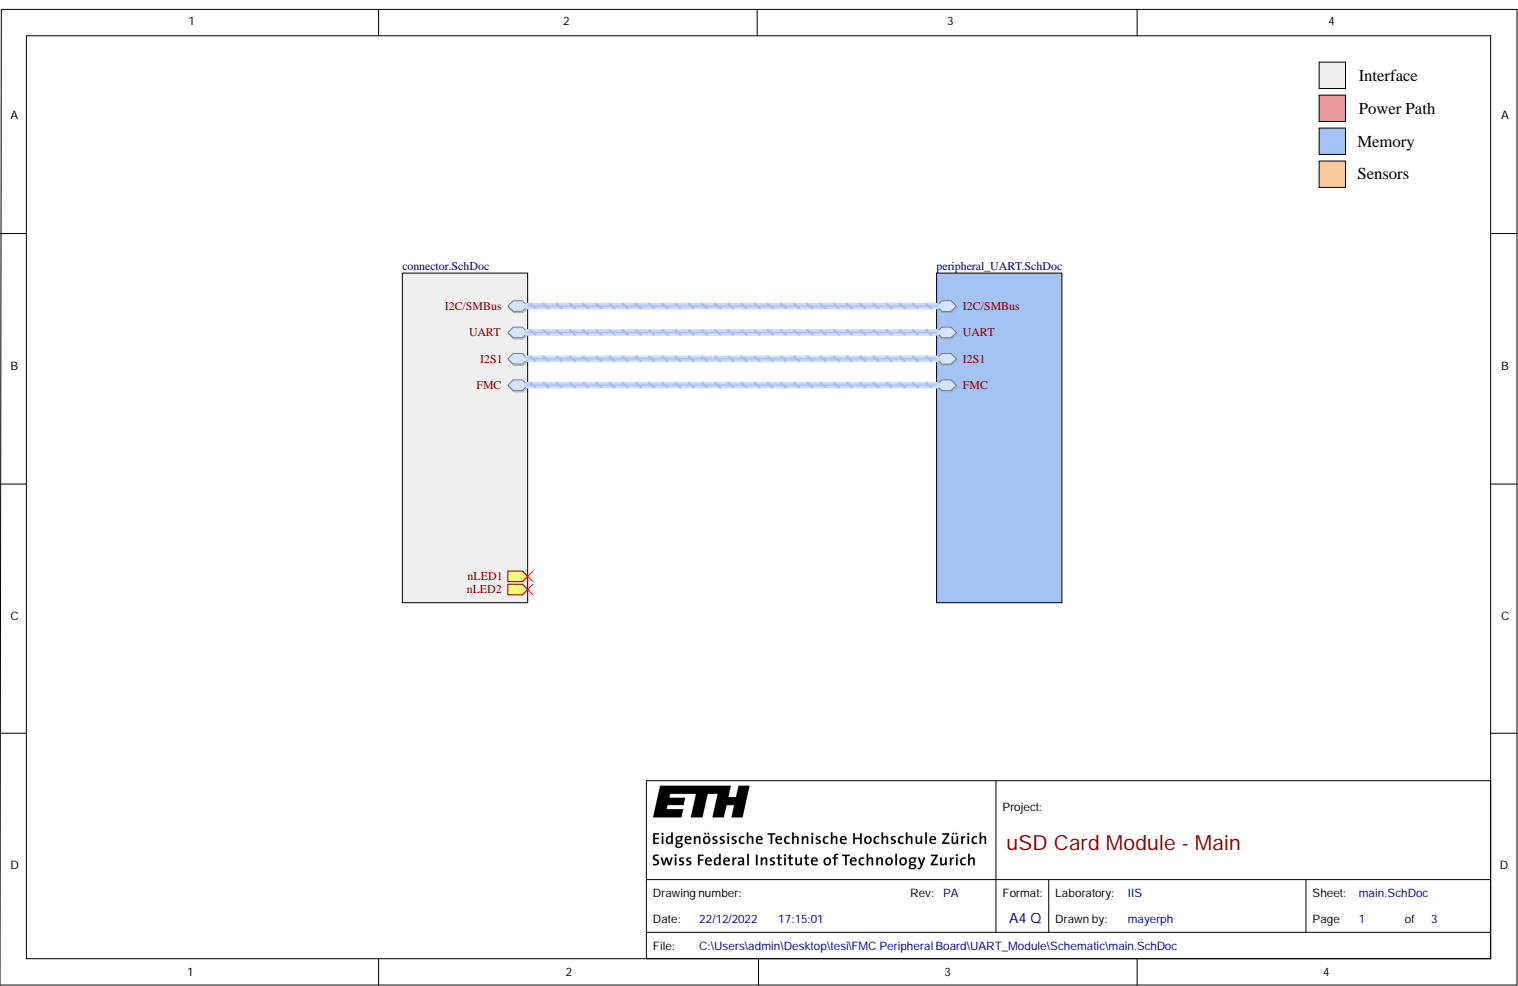
[picture p77: page 1]

Project: uSD Card Module - Main

Drawing number: Rev: PA Date: 17:15:01 | Format: A4 Q | Laboratory: IIS Drawn by: mayerph | Sheet: main.SchDoc Page 1 of 3

C:\Users\admin\Desktop\tesi\FMC Peripheral Board\UART_Module\Schematic\main.SchDoc

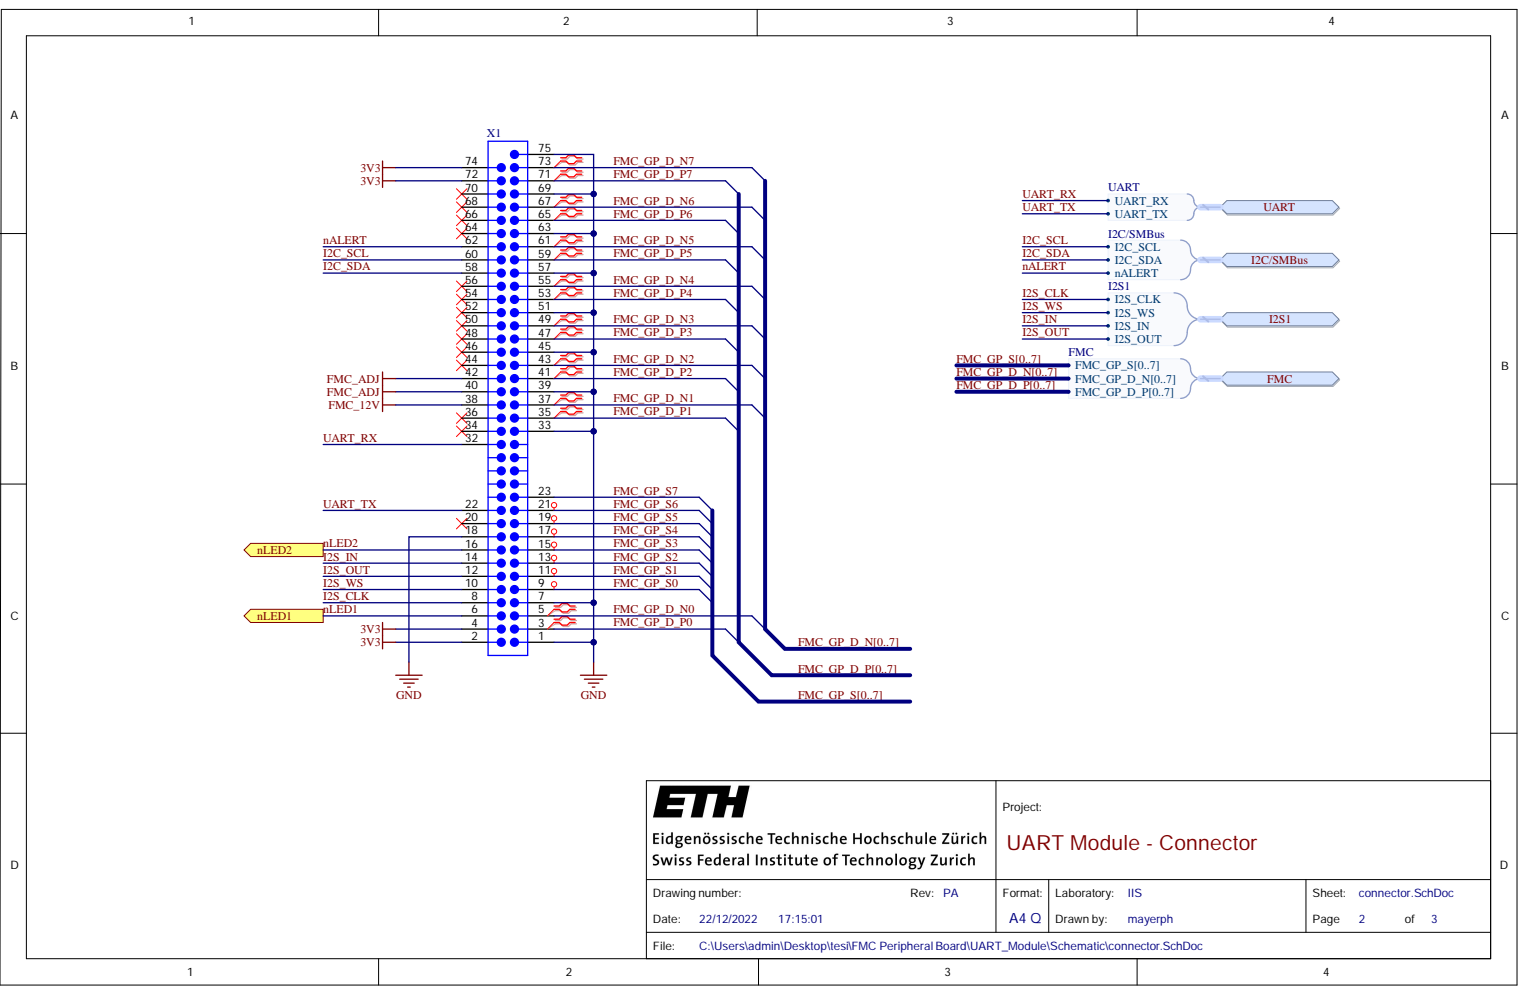
[picture p78: page 2]

Project: UAR T Mo d ule - C o n n e cto r

Drawin g n umb er: Rev: PA 2 1 | Forma t: A 4 Q | L a b oratory: IIS Drawn by: | Sh eet: co n n ector. SchDoc Page 2 of 3

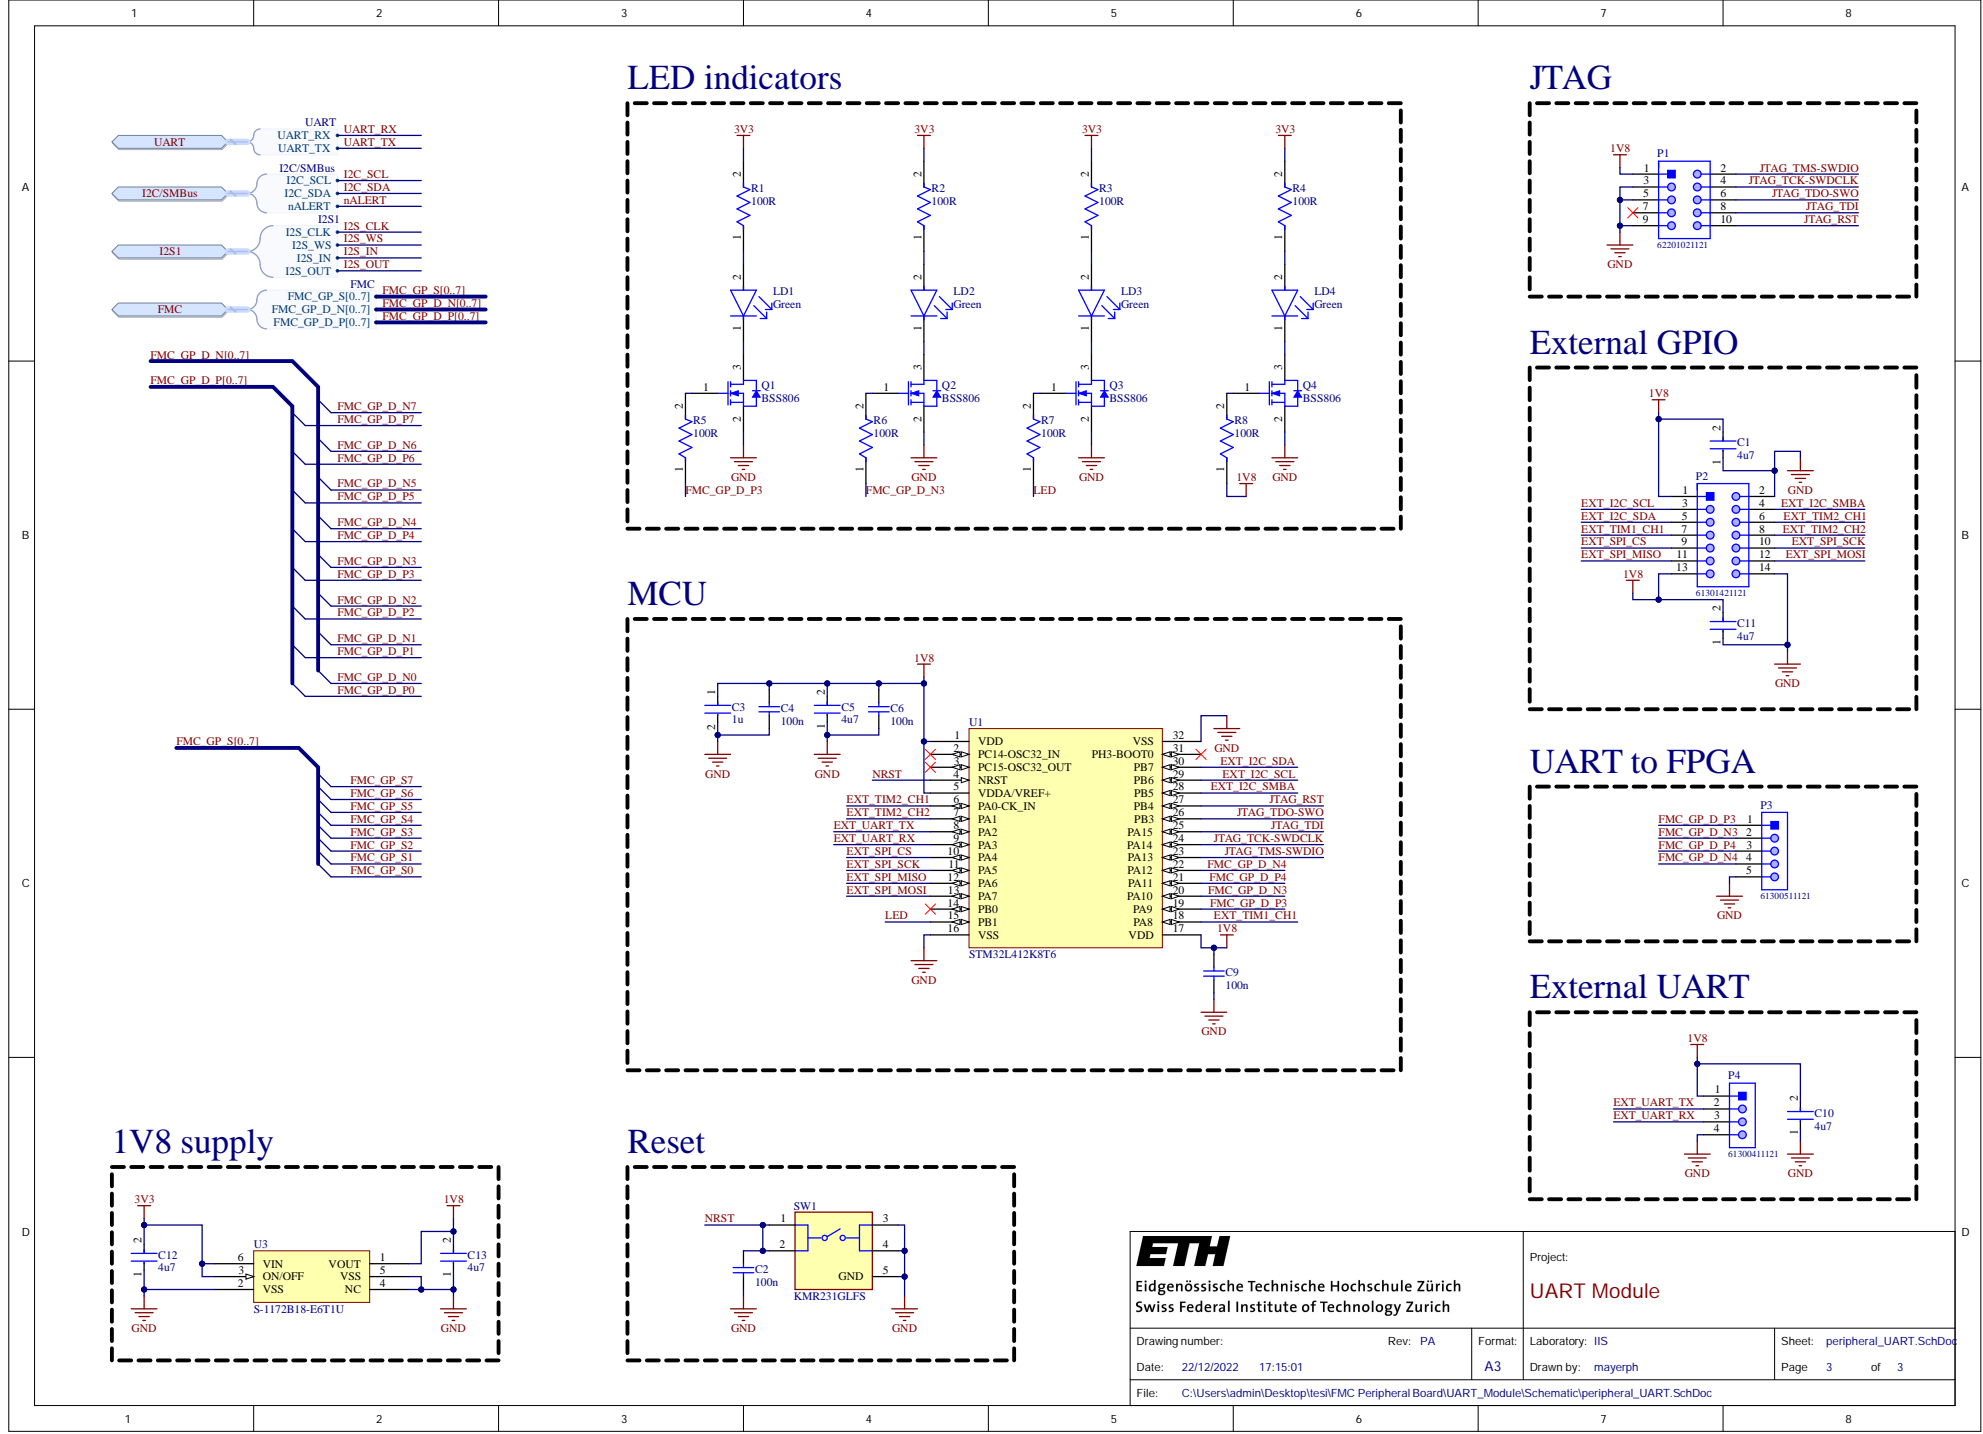
[picture p79: page 3]

4 | EXT_I2C_SCL
5 | EXT_I2C_SMBA

Project: UAR T Mo d ule

Drawin g n umb er: Rev: PA 2 1 | Forma t: A3 | L a b oratory: IIS Drawn by: | Sh eet: p erip h eral_UART.SchDoc Page 3 of 3
